pantojinho/StratosCore/docs/MECHANICAL_REQUIREMENTS.md

# Mechanical requirements

Target footprint approximately **80 x 60 mm**, with a **3D-printed enclosure containing the display and two removable 21700 cells**. The first verified fit study proposes an 84 x 60 mm PCB and about 37 mm enclosure thickness. See [mechanical/RF floorplan](MECHANICAL_RF_FLOORPLAN.md). These remain CAD starting envelopes.

Support two removable 21700 cells in a documented 2S holder. Nominal cell class is about 21 mm diameter x 70 mm length; actual selected cell, protection/button top, wrapper, contact travel and holder can exceed those values. A nominal 70 mm cell leaves only 10 mm along the 80 mm target for both contacts and walls. Two nominal diameters already consume 42 mm before separators/holders. Verify tolerance stacks before claiming fit.

A 21.7 mm cell beneath the 4.22 mm display candidate and 1.6 mm PCB consumes 27.52 mm before components, adhesive, gaps or walls. The dimensional reference holder is about 82.2 mm long, so a strict 80 mm board is not feasible. The marketplace holder shown by the owner is an unverified sample candidate until its drawing, wiring and contact ratings are confirmed. The display outline is documented, but FPC bend/connector geometry and sample fit still need verification. Do not freeze connector cutouts or stacked-board design from this arithmetic. Keep batteries away from antenna keepouts and evaluate magnetic bias.

## Required fit study

Build later dummy solids from verified drawings: module/antenna keepout, LCD glass/FPC/connector, cell(s)/holder/removal clearance, PCB/component heights, USB-C, microSD insertion/removal, two button actuators, GNSS antenna alternatives, LoRa U.FL pigtail/SMA bulkhead and ADS-B RF path. Check both orientations, fingers/grip, cable bends and access to recovery/test pads.

Provide positive cell retention, insulated contacts, reverse-insertion prevention, no wrapper damage, and a serviceable battery door. Account for vibration and drops. 3D-print material must be selected against measured internal heat and solar exposure; no flammability, ingress or impact rating is claimed.

SHT40 needs airflow and thermal isolation. BMP581 needs a controlled static pressure path; microphone needs an acoustic path. Rain/dust membranes and slots must be designed with sensor response and manufacturability, not generic decorative openings. Provide antenna strain relief; do not let pigtails cross the ESP module antenna region casually.

Deliverables before placement: dimensioned two-cell envelope and tolerance table, sensor/antenna keepout map, connector access review and printed fit dummy. Files in `mechanical/` are placeholders now; no fabricated STEP/STL is included.
