pantojinho/StratosCore/docs/ASTRA_AGENT_REVIEW_2026_09_24.md

# Astra review of the agent handover — 2026-09-24

Reviewed base: `912894b7dc1f4f4c764267f3bca375b8237b2e48`. Scope: repository and handover consistency, fresh candidate ERC/DRC, selected physical pad/net inventory, cost arithmetic and targeted primary-source checks. This is an independent review of the received agent claims, not a complete electrical, RF, mechanical or manufacturing qualification. No CAD geometry, circuit or project rule was changed.

## Fresh checks

KiCad **10.0.6** loaded the candidate and ran DRC with schematic parity, all track errors and an in-memory zone refill. The board was not saved. The tracked board SHA-256 is `6b77691bea8247bafd36f409d22fdd4d639e2af1f88b8735b518b835c3d2bd30`.

| Check | Observed result |
| --- | --- |
| DRC violations | 328 reported: 209 errors (10 clearance + 199 mask bridges), 119 warnings (118 silkscreen + 1 dangling track) |
| Unconnected items, separate from the violations array | 2 errors, `LORA_RFO` and `LORA_RFI_P` |
| Schematic parity | 0 reported findings |
| ERC | 1 error and 5 warnings; one warning is a library-symbol mismatch |
| Report limits and coverage | 199 mask findings is a reporting lower bound. Five DRC check categories remain disabled in project settings; zero shorts/parity findings do not establish complete correctness |
| Candidate inventory | 277 footprints; U7 pad 17 is GND, 1.68 x 1.68 mm, and its selected footprint is RGT0016C |

Evidence: [DRC with refilled zones](../candidates/claude-oneshot-revA/kicad/reports/astra_audit_2026-09-24/drc_refilled.json), [ERC](../candidates/claude-oneshot-revA/kicad/reports/astra_audit_2026-09-24/erc.json), [pad/net/zone inventory and arithmetic](../candidates/claude-oneshot-revA/kicad/reports/astra_audit_2026-09-24/inventory.json). The new DRC type counts match the tracked September 23 JSON, including **118**, not 117, silkscreen findings.

## Findings and dispositions

| ID | Finding supported by this review | Disposition |
| --- | --- | --- |
| AR01 — major | The candidate README's DRC-error row omitted 10 clearance errors. The received notes call them cosmetic or accepted for prototype. Fresh DRC reports different-net GND/EFUSE_ILM and GND/TP1 VBUS clearance violations, including 0.0773 mm actual against 0.1270 mm required | Correct documentation; keep T3 open. Continuing refinement is not acceptance of these defects |
| AR02 — major | The GND note claims a GND fill island acquired VBUS from TP1 and recommends ignoring zone net names. The actual clearance report identifies **TP1 pad 1**, not a VBUS zone. The inventory contains GND and 3V3_MAIN copper zones, no VBUS zone; a full refill did not remove the violations | Retract the zone-renaming explanation and routing heuristic. Inspect object type, assigned net, UUID and layer; never relabel foreign copper by nearby anchors |
| AR03 — major | D-MASK says S1 needs no assembler query, premium or delay and will retire all 199 findings. The underlying source note explicitly retains assembler/stencil questions and a BMP581 recommendation conflict. A pad-dam calculation alone proves none of those conclusions | Keep S1 as the recorded candidate direction, with implementation and acceptance pending. Do not treat a mask edit as resolving under-sensor routing or all DRC defects |
| AR04 — major | A5/A8 are not implemented: U13 pad 11 remains `EXP_CS_N`; J4 pad 1 remains `LCD_RST_CTRL`. A6 (`SX_NRESET` on U13 pad 13) and A7 (`RP_RUN` on pad 17) already exist in the candidate, but firmware sink-only behavior and the rail decision are not proven by connectivity | Distinguish physical implementation from the decision record. The A8 record specifies a **10 kohm pull-down**, not a pull-up; preserve that polarity and sample-validation condition |
| AR05 — cost evidence | Recalculated the supplied 14 IC prices: USD 59.1021; adding the listed RF/display prices yields USD 113.0461; substituting the unavailable cheaper IMU yields USD 97.9981 = BRL 503.85 at the recorded FX. Arithmetic agrees with the snapshot | This is a partial channel-price scenario, not a globally proven minimum or current quote. Some selected parts have zero stock. BRL 691–726 includes estimated PCB/assembly charges, not import taxes. D24 stays open; no automatic target revision |
| AR06 — reporting | Received notes say 117 silk findings; the tracked and fresh JSON both give 36 overlap + 76 over-copper + 6 edge = 118. The statement that nothing is hidden is too broad: five DRC check categories are disabled | Correct the count and state the configured coverage. No project rules were weakened or changed during this review |
| AR07 — traceability | The candidate decision record links GPIO and cost evidence from the wrong directory. Its final paragraph also suggests the owner must do a manual pass before Astra can act | Repair the evidence links; Astra owns review and execution coordination now. Historical task IDs remain valid |
| AR08 — confirmed with limits | Ground reconnection claims are consistent with fresh DRC reporting only the two LoRa opens. The U7 exposed-pad dimensions and footprint identifier are present in the file | Confirm these narrow facts. They do not validate return-path quality, thermal-via adequacy, power loops, RF behavior or every manufacturer land dimension |

The project-wide documentation also contained obsolete Sol-led / Astra-only-final-CAD instructions. The owner's explicit September 24 direction supersedes them; [D20](DECISIONS.md) and [project control](ASTRA_PROJECT_CONTROL.md) now record Astra's active leadership and delegated worker roles.

## Primary-source spot checks

- **KiCad 10.0 PCB Editor manual**, sections "Working with zones", "Drawing zones" and "Clearances & pad connections", reviewed 2026-09-24: zones have a selected net, keep clearance from other nets and connect according to same-net pad settings. This does not support automatically renaming a GND island to VBUS from an adjacent pad. [Official manual](https://docs.kicad.org/10.0/en/pcbnew/pcbnew.html).
- **Bosch BST-BMP581-DS004-13, revision 1.13, April 2025**, section 8.2, page 69, reviewed 2026-09-24: recommends no traces/vias or solder mask under the sensor, at least 200 micrometres pad separation and 20 micrometres horizontal mask clearance per side. S1's intervening mask therefore needs documented engineering/process disposition; a feasible nominal dam width does not establish manufacturer-conforming assembly. [Manufacturer datasheet](https://www.bosch-sensortec.com/media/boschsensortec/downloads/datasheets/bst-bmp581-ds004.pdf).

No fresh supplier prices, stock, factory commitments, TDK/TI package acceptance or physical performance measurements are claimed by this review. Prior source transcriptions outside these spot checks remain dated evidence requiring their planned reviews.

## Reproduction and next actions

From the repository root, with KiCad 10.0.6 on PATH:

```text
kicad-cli pcb drc --format json --schematic-parity --all-track-errors --refill-zones -o candidates/claude-oneshot-revA/kicad/reports/astra_audit_2026-09-24/drc_refilled.json candidates/claude-oneshot-revA/kicad/StratosCore_Claude.kicad_pcb
kicad-cli sch erc --format json -o candidates/claude-oneshot-revA/kicad/reports/astra_audit_2026-09-24/erc.json candidates/claude-oneshot-revA/kicad/StratosCore_Claude.kicad_sch
python candidates/claude-oneshot-revA/tools/audit_handover.py
```

Use KiCad's bundled Python for the last command. The script reads the PCB and supplied report/price data and writes only the inventory report. DRC descriptions can be localized; type keys and object UUIDs are the comparison evidence.

Successful command execution means reports were generated, not that ERC/DRC passed: the commands above do not request violation-based exit codes. Relative links in the changed Markdown files and `git diff --check` were checked; no tracked KiCad board, schematic, library or project-settings file changed in this audit.

Astra retains T1–T8 and the existing subsystem gates. Next CAD work must resolve actual U3 clearance geometry, validate mask/under-sensor routing, implement A5/A8 after their dependencies, verify A6/A7 behavior, and review power/RF/mechanical details in the GUI against exact source drawings. O05 qualified battery review, controlled display samples, stackup/factory confirmation and independent implementation review remain open. This review does not approve manufacture or energizing.
