pantojinho/StratosCore/docs/OPEN_QUESTIONS.md

# Open questions and closure evidence

This file lists unresolved work only. [Project status](PROJECT_STATUS.md) sets priority; [decisions](DECISIONS.md) records accepted and rejected choices. An accepted direction remains open here when exact engineering or test evidence is still required.

2026-09-24 coordination: Astra now owns engineering closure and delegates bounded tasks to other agents. [The independent handover review](ASTRA_AGENT_REVIEW_2026_09_24.md) confirms that candidate clearance/mask defects and digital implementation gaps remain open; reported proxy decisions do not close O05, display/process, RF, interface or D24 cost evidence gates. [Project control](ASTRA_PROJECT_CONTROL.md) tracks the T1–T8 follow-up queue.

| ID | Status | Type / owner | Question or required closure evidence |
| --- | --- | --- | --- |
| O01 | THREE-LINE MODE PREPARED + SAMPLE GATE | Display / procurement + CAD | Revision-J verifies write-only three-line `101`; obtain controlled TFT-power/FPC clarification, verify XF3M fit/mode on two labeled samples, independently review connector/translator CAD and prototype TPS61169 current, brightness, faults, EMI, touch and shared-bus behavior |
| O03 | PDN CALCULATION CLOSED 2026-09-22; RF/OWNER REVIEW OPEN | GNSS / RF + CAD | GNSS-01 (PR #158) closed the PDN series-impedance budget against the 0.2 ohm u-blox limit (~0.14-0.22 ohm worst, DCR<=0.15 ohm bead fallback) and confirmed the 18-pin net/application table complete: always-on tied 3.3 V VCC/V_IO; open V_BCKP/RESET_N/EXTINT; passive `FXP611.07.0092C` through `U.FL-R-SMT-1(60)` and `TPD1E0B04DPYR`, with no RF bias. Remaining: independent RF/PDN review, owner/RF acceptance of the PROPOSED supply/backup/reset choices, footprints, placement/routing constraints and VNA/test provisions. Cold-start/PPS/AIR4/coexistence and physical VNA results are post-PCBA DVT evidence |
| O04 | PRE-ASTRA DESIGN GATE | ADS-B / RF | Before Astra, freeze the BLB01/TA2003A/ADL5513/MCP6566 topology, exact parts, bias/threshold network, stackup rules, simulation/review evidence and conducted-test provisions for sensitivity, blockers, gain, pulse timing and coexistence. Physical measurements are post-PCBA DVT evidence |
| O05 | OWNER ACCEPTED; REVIEW BLOCKED | Power / qualified reviewer | Resolve BQ25887 autonomous charge after reset, fail-safe `CD` gating, charger/common-protector ground and cutoff recovery, charge-under-load termination, exact holder/cells/FETs/fuse/NTCs and fault limits before schematic commitment or energizing |
| O06 | USB INPUT + RAIL INVENTORY CLOSED 2026-09-22; CHARGER ENGINEERING OPEN | Power / Sol + qualified reviewer | D21 requires operation while charging. PWR-02 (PR #147) closed the TPS259474L eFuse network (RILM/UVLO/OVLO/dVdt) and the TUSB320LAI GPIO-mode default-current-only sink policy; ITIMER remains TBD pending the charger's worst-case inrush/input-capacitance transient. PWR-04 (PR #157) closed all `3V3_MAIN` rail loads and startup sequencing (~1,413 mA simultaneous worst-case, 59% of the 3 A buck rating with margin). Remaining: select exact holder/protection topology and calculate BQ25887 charger setpoint, buck, balancing, state estimation and charge-under-load termination. No batteryless operation or USB PD is proposed |
| O07 | AUDIO NETS RECONCILED AS PROPOSAL; APPLICATION/FOOTPRINT REVIEW OPEN | Audio/power/CAD + test | AUD-01 (PR #159) pinned TXU0202 channel directions. The 2026-09-22 [audio-domain review](AUDIO_DOMAIN_REVIEW.md) found shared `1V8_LOGIC` versus switched-audio inconsistency. Integrator reconciled the preferred net plan: keep TFT on `1V8_LOGIC`; switch only T5838 VDD and TXU0202 VCCB/OE via `1V8_AUDIO_SW`. Exact TPS22918 CT/QOD/ramp/drop, off-state pins and boot sequence remain before schematic entry; do not treat the candidate as a frozen circuit. The TXU0202 footprint requires independent exact-MPN review and T5838 acoustic land is deferred; port/gasket, optional DNP and test plan remain. PDM/RF measurements are post-PCBA evidence |
| O08 | PROTOTYPE GATE | Mechanical | Verify the 84 x 60 mm PCB and approximately 88 x 64 x 37 mm enclosure with exact component drawings and a printed fit dummy |
| O09 | PREFERRED INTERCONNECT - U.FL CAD REVIEWED | RF/mechanical / RF + CAD | Review P20/P25; U.FL copper/paste and board-cut-out comparison is complete; independently compare the CAB.721 drawing, obtain U.FL assembler approval, fit all cables/antenna in the enclosure dummy, calculate/VNA-check each 50-ohm path and verify port labeling, tool access, strain relief and coexistence |
| O10 | STACK VERIFIED; SOLVER GATE OPEN | PCB/manufacturer | JLCPCB officially documents JLC04161H-3313 replacing the former 2313 (same thickness/Dk 4.1, verified 2026-09-17 with candidate geometries in PCB_STACKUP.md). Before Astra routing, obtain reproducible factory-solver 50/90-ohm geometries and tolerances. The actual order ticket, coupon and TDR are post-layout manufacturing controls |
| O11 | ENGINEERING ANALYSIS CLOSED 2026-09-22; OFF-STATE REVIEW REMAINS | Hardware / Sol + CAD + test | D22/P26 applied via PR #140: GPIO/net map updated with the TUSB320LAI GPIO-mode wiring (SLLSEQ8D Rev D), reduced participant set evaluated, pull-up 2.2 k ohm +/-1% proposed with a window non-empty to the 400 pF ceiling, expansion-cable limit declared <=150 pF and stuck-bus recovery assigned. DIG-03 (PR #149 + polarity fix #152) fixed the switched-domain default: pull-down + active-high EN per TPS22918 leaves every domain OFF through expander reset/hang/power loss (`*_EN` net rename recorded for Astra). Remaining: per-device off-state review (touch, BQ25887, switched domains), post-placement `Cb` recount, independent net-matrix review (SYS-04) and the post-PCBA rise-time/VOL validation |
| O12 | HOST CONTRACT TESTED; PRE-ASTRA INTERFACE GATED | RP2040 interface / Sol | The host-side UART framing behavior passes 20 framing tests plus the four existing capture-model tests: fixed payload shapes, CRC16-CCITT, rolling sequence, 64-bit timestamp reconstruction, declared overflow, resynchronization after garbage/corrupt headers/CRC and a fragmented 200-contact stream. [SYS-03 contract](CONCURRENCY_CONTRACT.md) calculates 921600-baud/8N1 line headroom and UART blackout buffering but leaves actual DMA/PIO/ring sizing and timing TBD. Before Astra, freeze pins, clocks, PIO/DMA contract, exact burst/throughput and test access. Real-hardware sustained-link tests remain post-PCBA |
| O13 | 8 H OWNER TARGET ACCEPTED; ANALYTICAL BUDGET CONSISTENT, MEASUREMENT OPEN | Power/product | D25 sets 8 h on the two-cell pair for primary use. The conservative 1.935 W FLIGHT allowance gives an estimated 10.72 h with two example 5 Ah cells under the documented 80% usable/90% conversion assumptions, so the model clears 8 h but proves no actual runtime. Before Astra, close primary-use duty/brightness and cell/thermal assumptions; real rail efficiency, cell behavior and full-profile runtime are measured post-PCBA |
| O14 | DEFERRED | Firmware/license | Select firmware framework and define MeshCore mode/port/dependencies after the hardware baseline; complete transitive license audit |
| O15 | CONTINUOUS | Maintainer/license reviewer | Record any reused circuit/code at file level; resolve ADSBee GPL and avBadge uncertainty before reuse |
| O16 | BMP581 RETAINED; INDICATIVE 10,000 FT TEST/ENVIRONMENT OPEN | Product/test | D25/D29 now use ~10,000 ft as the realistic case and keep BMP581 as secondary indicative altitude/vario. The former 30,000 ft guarantee was withdrawn; [P27](BAROMETER_30K_PROPOSAL.md) was rejected. Define actual board temperature, reference pressure/calibration, vent behavior, bench pressure/vario test and invalid/out-of-range display/logging. Assess exposed flight/balloon dynamics and temperature separately; do not claim 30,000 ft coverage |
| O17 | DEFERRED | Product/firmware | Set acquisition rates, SD capacity, audio format and allowed data loss after hardware interfaces and power profiles are stable |
| O18 | OWNER INPUT + RF TEST | ADS-B/product | Define sensitivity, range, contact/stale-time targets and a repeatable conducted/field test plan |
| O19 | CORRECTED CANDIDATES; INDEPENDENT / ASSEMBLER REVIEW OPEN | Sensors/procurement + CAD | The 2026-09-23 [correction record](FOOTPRINT_CORRECTIONS_2026_09_23.md) supersedes the old MMC5983MA/BMP581 dimensional-pass claims: radial land centers and provisional paste are repaired, top-view pin maps rechecked, and pairwise copper gaps pass at 0.200 mm. Independently review the revised files and assembler mask/paste/stencil choices. SNS-02 placement constraints remain in the floorplan; final routing, magnetic/pressure-port placement and fit-dummy checks remain open |
| O20 | IN PROGRESS - EXACT PACKAGE REVIEW | Digital/GNSS/RF CAD | See [corrections and rejected drafts](FOOTPRINT_CORRECTIONS_2026_09_23.md). The old TXU0202 DGS and TPS259474L RPU files must not be assigned. Exact DCU copper was rederived and checked; exact RPW polygon/stencil still needs closure. The original TCA9535 body is 4.4 x 7.8 mm, not the unpublished 6.4 mm draft. Re-review all DIG-04 parts against drawings, reconcile library/process gates and finish deferred USB4105/BM12B/SKSCLCE010/ST1633I/T5838 footprints. DIG-01/02 electrical work and DM3/test-access gates retain their separate scope |
| O21 | OWNER CLASSIFICATION ACCEPTED; REGULATORY PLAN OPEN | Regulatory/owner | D23 defines Rev A as a personal, non-commercial, open-community hobby prototype. Determine the applicable ANATEL operating path for 915 MHz TX and the 2.4 GHz/1.575 GHz/1.090 GHz receivers; the classification does not itself authorize radio operation |
| O22 | OWNER HOBBY USE CASES ACCEPTED; FLIGHT PLAN OPEN | Regulatory/owner | D25 includes desk/car/protected unpressurized cabin use and possible experimental drone, model-aircraft, balloon, ultralight, hang-glider and paramotor installation. Determine the applicable aviation/balloon rules, tracking, authorization and recovery obligations for any actual flight after each installation envelope and built mass are known; no design target mass is imposed |
| O23 | ACCOUNTING BOUNDARY ACCEPTED; QUOTES OPEN | Product/procurement | D24 sets an average ceiling of BRL 200 per unit for the first five Chinese PCBAs including display/touch, excluding local cells/enclosure, freight and taxes. Obtain actual five-unit assembly/display quotes and record whether the target is feasible without silently removing locked Rev A functions |
| O25 | OWNER POLICY ACCEPTED; LOCAL PLAN OPEN | Manufacturing/test | D28 selects factory PCBA assembly only, then local USB-C flashing and testing with no factory firmware or credentials. Define the local programming fixture/procedure and board-identification method; retain accessible SWD recovery |
| O27 | PRE-ASTRA ENGINEERING BASELINE | Sourcing/BOM | Convert `bom/preliminary_bom.csv` into a frozen engineering parts baseline: every fitted/DNP item and passive needs exact specification, package, approved footprint, planned quantity and sourcing status. The [2026-09-22 gap audit](BOM_BASELINE_GAP_AUDIT.md) verified 58 rows, no quantity column, 7 literal `MPN=TBD` rows plus family-only `CELL_PROTECTION`, 37 `JLCPCB/LCSC Part Number=TBD` rows (correcting the earlier 36), and an incomplete aggregate `PASSIVES_DEBUG` row. BOM-02 (PR #168) recorded 6 dated SNAPSHOT and 19 authorized-channel CHANNEL-ONLY groups; these are not current five-unit quotes or assembler acceptance. Astra produces annotated references/quantities only after the engineering baseline; final orderable BOM follows review |
| O28 | PRE-PLACEMENT MATRIX FROZEN 2026-09-22; POST-LAYOUT FIXTURE REVIEW OPEN | Test/DFT | DFT-01 (PR #161) froze the 17-row pre-placement DFT coverage matrix in `manufacturing/test/README.md`: nets requiring pads, programming/SWD/BOOTSEL access, RF injection, pad family/minimum geometry, permitted face, fixture pitch, current limits and the rail/current measurement points feeding O13, all traced to accepted deliverables (DIG-01/02/03, PWR-02/04, GNSS-01, AUD-01, SYS-01, P25). Protection-FET access deliberately not defined (O05/PWR-03). Remaining: Astra assigns references/coordinates during placement; physical probe access and fixture feasibility are reviewed after layout; production screening limits need measured data |

## Recently closed owner decisions

| ID | Closed | Outcome |
| --- | --- | --- |
| O02 / P07 | 2026-09-13 | Owner replaced ATGM332D-5NR32 with MAX-M10S-00B for the balloon altitude envelope |
| P08 / P14 | 2026-09-13 | Owner rejected independent 1S bays and accepted two removable matched 21700 cells in 2S with one balanced charger and common protection direction |
| D21 / O06 policy | 2026-09-21 | Owner requires normal operation while USB charging; exact safe charge-under-load design remains open |
| D22 / P26 policy | 2026-09-21 | Owner accepted 100 kHz shared I2C and TUSB320LAI GPIO mode; SYS-01 implements and reviews the electrical details |
| D23 | 2026-09-21 | Owner classified Rev A as a personal, non-commercial, open-community hobby prototype |
| D26 / O24 | 2026-09-21 | Owner will source cells locally; shipping the prototype with cells is outside the current scope |
| D27 / O26 | 2026-09-21 | Owner requires no conformal coating, ingress qualification or special environmental protection for Rev A |

P14 is closed as a product direction but O05/O06 remain open engineering and review gates. The qualified electrical/battery review is mandatory before the exact topology is frozen, entered as a committed schematic or energized.
