pantojinho/StratosCore/docs/PROJECT_STATUS.md

# Project status

Last updated: 2026-09-24. Current phase: **Astra-led hardware engineering closure and candidate refinement**.

Astra has already assumed full technical leadership, coordination, review and integration of StratosCore, as accepted by the owner in revised D20. Claude, Hermes, Sol and other AI agents execute bounded tasks delegated by Astra. The immediate objective remains exact component/application/interface closure, candidate correction and hardware/PCBA readiness. [Astra project control and agent handover](ASTRA_PROJECT_CONTROL.md) records the received summary, its evidence boundaries and the T1–T8 candidate queue.

Execution is coordinated through the [Astra-led engineering workboard](PRE_ASTRA_WORKBOARD.md). Parallel agents follow the [swarm protocol](SWARM_PROTOCOL.md); Astra as integrator reconciles shared status, decision, open-question, handoff and BOM files. The reusable [Astra execution prompt](ASTRA_EXECUTION_PROMPT.md) remains **NOT READY** for final frozen-baseline implementation until its input manifest and every handoff gate are complete.

## Completed and verified

| Area | Current result | Evidence boundary |
| --- | --- | --- |
| Repository foundation | Licensing, contribution rules, source/reuse tracking and direct-to-main workflow established | Does not release hardware for manufacture |
| Rev A product baseline | Compute, display class, sensors, LoRa, ADS-B/RP2040, storage, audio provision, expansion and four-layer construction recorded | Exact open parts remain below |
| Display evidence | C1 serial straps verified; write-only three-line `101` preferred; exact XF3M lands and AXC/LVC/backlight starting circuits documented | Controlled TFT power/FPC clarification, samples, connector footprints, independent CAD and prototype tests still gate release |
| GNSS product decision | MAX-M10S-00B accepted; pin/application evidence and P20 passive antenna/U.FL/ESD proposal reviewed; manufacturer-derived copper/mask/T-paste footprint parses in KiCad, passes its automated geometry audit and completed an independent dimensional review | Assembler paste approval, RF/PDN review, antenna fit and prototype tests remain |
| Battery product decision | Two removable matched 21700 cells in 2S; one balanced charger and common protection direction accepted | Exact circuit needs qualified electrical/battery review |
| Owner operating/product inputs | Operation while charging; 100 kHz shared I2C with TUSB320LAI in GPIO mode; personal non-commercial community prototype; five-unit BRL 200 average PCBA-plus-display/touch target; desk/car/protected unpressurized cabin and possible experimental hobby flight uses; ~10,000 ft realistic, 30,000 ft exploratory; BMP581 indicative backup; 8 h minimum on two 21700 cells; local USB-C flashing/testing; locally sourced cells; no coating/ingress qualification | P27 LPS22HBTR replacement rejected; sensor temperature, exposed-flight/balloon envelopes, ADS-B targets, cost feasibility and local test procedure remain open |
| ESP32 compute | ESP32-S3-WROOM-1-N16R8 entry, decoupling/reset and complete GPIO allocation present in KiCad | Board-level concurrency and boot-state validation remain |
| Sensors | All four logical entries are present. A fresh drawing comparison found and corrected MMC5983MA/BMP581 baseline land geometry errors in `9e909f3`; see the [correction evidence](FOOTPRINT_CORRECTIONS_2026_09_23.md). SNS-02 (PR #167) froze dimensioned, zoned placement constraints in `MECHANICAL_RF_FLOORPLAN.md`. A [BMP581 validation plan](BMP581_VALIDATION_PLAN.md) distinguishes indicative ~10,000 ft design/test work from post-PCBA measurement | Independent review of corrected files, candidate embedded footprint reconciliation, assembler mask/paste disposition, proposed data-validity contract and fit-dummy/routing conformance remain |
| ADS-B digital feasibility | Host timing/CRC fixture passes four tests; UART framing behavior passes 20 additional host tests | UART throughput and RP2040 PIO/DMA hardware remain unproven; analog RF sensitivity is also open |
| Remaining support candidates | Exact candidates documented for main/quiet/1.8 V rails, PDM audio, USB-C/signal ESD, expansion, buttons, slow I/O and RF interconnects; historical parse/export and dimensional-review records exist, but the sensor/DCU/RPW defects mean those records do not establish blanket readiness. AUD-01 closed TXU0202 channel directions and mic supply/clock/acoustic evidence; later integration found its direct-`1V8_LOGIC` assignment conflicted with audio switching, so [AUD-02](AUDIO_DOMAIN_REVIEW.md) prefers a separate `1V8_AUDIO_SW` branch pending exact application review. DIG-04 (PR #164) added eight standard-package footprint candidates | DM3 enclosure/process closure, assembler approvals, audio switch CT/QOD/ramp/off-state, port/gasket (MECH-02/03), VBUS/protection and board tests remain open. The new exact-DCU candidate and remaining DIG-04 exact-MPN reviews plus five deferred footprints (USB4105, BM12B, SKSCLCE010, ST1633I, T5838) remain open |
| KiCad structure | Root plus eight sheets parse in KiCad 10; latest ERC has zero violations | Several sheets are intentional holds, not completed circuits |
| Mechanical planning | 84 x 60 mm PCB and about 88 x 64 x 37 mm two-cell enclosure are starting envelopes | Printed dummy, exact holder and display connector/sample fit remain |
| Manufacturing plan | Four-layer Chinese PCBA workflow and release gates documented. BOM-02 (PR #168) consolidated the per-MPN sourcing evidence register 2026-09-22 (`bom/SOURCING_EVIDENCE.md`): 6 dated SNAPSHOT rows plus 19 authorized-channel CHANNEL-ONLY groups, no fabricated stock/price. The [BOM gap audit](BOM_BASELINE_GAP_AUDIT.md) counted 58 planning rows, 7 literal MPN TBDs, family-only protection, 37 supplier-ID TBDs and no planned quantities | No Gerbers, CPL or engineering parts baseline exist yet; engineering baseline work is O27/BOM-01/03. DFT-01 froze 17-row pre-placement coverage; Astra still assigns references/coordinates. Purchase-time recheck remains authoritative; annotated/final orderable BOMs follow capture/review |

## Out-of-baseline comparison candidate (2026-09-23)

At the owner's explicit request, a complete one-shot KiCad candidate (12-sheet schematic, routed 4-layer 60 x 84 mm PCB, display/2S-cell/enclosure 3D) was generated in [`candidates/claude-oneshot-revA/`](../candidates/claude-oneshot-revA/README.md) for comparison with the Astra pass. It is **not** a baseline, does not close any gate below and keeps every unverified value `TBD`. Its [issue list](../candidates/claude-oneshot-revA/docs/ISSUES.md) records baseline defects that need independent review in `hardware/footprints/`: MMC5983MA pad centres (+/-1.05 mm vs MEMSIC 2.550 mm centre-to-centre, corner pads overlap), BMP581 pad centres (+/-0.6 mm vs Bosch 1.525 mm, 0.04 mm corner gap), TXU0202 footprint uses the DGS 3 x 3 mm package instead of DCU, TPS259474L footprint uses RPU instead of RPW, and BM12B-GHS-TBT is a vertical header, plus GPIO/expander allocation gaps (EXP_CS, SX1262 NRESET, RP2040 RUN, touch reset).

The initial 2026-09-23 KiCad 10.0.6 review recorded 1 ERC error/4 warnings, 1 DRC error/579 warnings, 11 unconnected items and zero schematic-parity issues; these are historical counts. The received handover at `912894b` reports 2 remaining LoRa connections, 0 shorts/parity findings, 10 U3 clearance findings, 199 reported mask bridges (report limit), 117 silkscreen findings and 1 dangling track. Astra's [independent September 24 review](ASTRA_AGENT_REVIEW_2026_09_24.md) reran DRC with zone refill and confirmed those counts except silkscreen: the correct total is 118. It recorded 209 DRC errors and 119 warnings, plus the two unconnected items separately, and ERC 1 error/5 warnings. A5/A8 and mask choices still need CAD implementation; A6/A7 connectivity exists but behavior and rail review remain open. The [independent review](CLAUDE_CANDIDATE_INDEPENDENT_REVIEW.md) and [bounded Astra candidate-refinement prompt](ASTRA_CANDIDATE_REFINEMENT_PROMPT.md) allow evidence-backed correction work now while the final execution handoff remains blocked.

## Remaining gates for final baseline implementation and release

| Priority | Gate | Astra-coordinated work and external dependencies | Closure evidence |
| ---: | --- | --- | --- |
| 1 | Exact display | Obtain controlled Orient TFT-power/FPC clarification and two labeled samples; validate provisional three-line `101` mode and XF3M fit; independently compare CAD and prototype translation/backlight | Verified footprints plus backlight, address, power, touch/readability, fault, EMI and shared-bus results |
| 2 | 2S power | D21 requires operation while charging and D26 fixes local removable cells. PWR-02 closed the USB input application 2026-09-22 (PR #147): TPS259474L eFuse network exact (RILM/UVLO/OVLO/dVdt; ITIMER TBD at O06), TUSB320LAI default-current-only policy fixed from GPIO-mode facts. PWR-04 closed the `3V3_MAIN` rail load inventory 2026-09-22 (PR #157): simultaneous worst-case ~1,413 mA (59% of the 3 A buck rating with 25% margin), every row sourced or declared ALLOW, regulator passives pinned and sequencing recorded. Remaining: accept exact cell/holder; resolve BQ25887 autonomous-start hardware gating, charger/protector ground/cutoff conflict and charge-under-load termination; close protection/FET/fuse/NTCs, buck, state estimation and every fault state | Qualified reviewer signs the complete schematic plan and fault limits before KiCad commitment |
| 3 | GNSS implementation package | GNSS-01 closed the MAX-M10S PDN calculation 2026-09-22 (PR #158): series-impedance budget against the 0.2 ohm u-blox limit (~0.14-0.22 ohm worst, DCR<=0.15 ohm bead fallback), module-local capacitance and soft-start ramp disposition; 18-pin net/application table confirmed complete. Obtain assembler approval of the independently reviewed MAX-M10S T-paste pattern; obtain independent RF/PDN review and owner/RF acceptance of the PROPOSED supply/backup/reset choices; close remaining RF calculations, keepout and test provisions. Physical VNA/cold-start/PPS/AIR4/coexistence results remain post-PCBA | Accepted choices, independently reviewed footprint, antenna fit/layout constraints and executable validation plan |
| 4 | Remaining digital parts | Datasheet-level evidence closed 2026-09-17 (W25Q JVSIQ ordering/QE/BOOTSEL/XIP, RP2040 boot/circuit, ABM8-272-T3 reference circuit). DIG-01 closed the RP2040 reset/BOOTSEL/SWD/oscillator circuit 2026-09-22 (PR #144). DIG-03 closed the TCA9535 16-port map 2026-09-22 (PR #149 + polarity fix #152): pull-down + active-high EN per TPS22918 leaves every switched domain OFF through expander reset/hang/power loss. DIG-02 closed microSD power/signal/ESD/card-detect/power-fail 2026-09-22 (PR #154): switched `3V3_SD` behind the DIG-03 enable, SPI-mode SD_CS->DAT3 mapping, socket-edge ESD array (device-level claim only). AUD-01 closed the T5838/TXU0202 audio application 2026-09-22 (PR #159): pin-complete translator channel directions, `1V8_LOGIC`-referenced OE rail-valid policy, mic clock window (2.0-3.7 MHz) and current input (310/340 uA typ/max), with DS section 9 acoustic land/hole/paste rules handed to DIG-04 verbatim. DFT-01 froze the pre-placement DFT coverage matrix 2026-09-22 (PR #161, O28). DIG-04 delivered the standard-package support-footprint set 2026-09-22 (PR #164), but exact-package acceptance was reopened on 2026-09-23 (see the correction record): all 17 project footprints parse/export in KiCad 10.0.6, eight new candidates carry per-file provenance to the copied KiCad-library source and TI package drawing class, five custom/connector footprints (USB4105, BM12B-GHS-TBT, SKSCLCE010, ST1633I, T5838 acoustic land) deliberately deferred. Before final baseline implementation, close DM3 enclosure/process, residual U.FL process/tool gates, per-pin off-state proof, insertion-surge measurement (PWR-04), the exact-MPN second pass on the eight new DIG-04 footprints, the five deferred footprints and Astra reference/coordinate assignment for the DFT matrix. Physical bench tests remain post-PCBA | Orderable reviewed MPNs, pin maps, footprints, interface/voltage evidence and test provisions |
| 5 | Sensors | ICM-42688-P retains its recorded dimensional review. MMC5983MA/BMP581 land centers were corrected after the old review missed defects; independent review of the revised files and assembler process approval remain open. SNS-02 froze placement constraints 2026-09-22 (PR #167). D29 retains BMP581 as an indicative backup for ~10,000 ft realistic use; 30,000 ft is exploratory. [BMP581 validation plan](BMP581_VALIDATION_PLAN.md) drafts pressure/vario and invalid-data tests. [P27](BAROMETER_30K_PROPOSAL.md) is rejected history | Review/accept validity contract, sensor environment, assembler approval and fit-dummy/routing conformance. Physical pressure/vario characterization is post-PCBA |
| 6 | LoRa RF | AN1200.40 Rev 1.1 evidence recorded: E449V01A 4-layer TCXO design proposed as starting topology, matching/notch/pi-filter topology and RX balun documented, DC-DC + crystal proposal with TCXO/DIO3 fallback, PE4259-class switch proposal, conducted test outline. Remaining: exact E449 regional BOM values (drawing-embedded) and RF CAD | Reference revision BOM values, independent CAD, simulation/stackup inputs and conducted-test plan |
| 7 | ADS-B RF | BLB01/TA2003A/ADL5513/MCP6566 bias and loss figures transcribed. ADSB-01 (PR #142) froze the base `MCP6566T-E/OT` pin map and a proposed 2.2 kohm pull-up; R/U variants are non-drop-in alternatives. Before final baseline implementation, close the threshold (OWN-09), remaining topology, simulation, stackup rules and conducted-test provisions. Physical RF measurements remain post-PCBA | RF review plus testable schematic, simulation evidence and conducted acceptance limits |
| 8 | PCB/mechanical inputs | JLC04161H-3313 stack verified from official JLCPCB pages 2026-09-17 (3313 replaced 2313, same thickness/Dk; candidate 50/90-ohm geometries computed and recorded in PCB_STACKUP.md). D27 selects no coating or ingress qualification. Before final baseline implementation, obtain factory-solver impedance geometry, outline/connectors/keepouts and fit dummy. The actual order ticket, coupon and TDR follow layout | Frozen stack/solver rules and signed mechanical fit review |
| 9 | System-level electrical review | D22/P26 applied 2026-09-22 (PR #140): 100 kHz shared I2C with TUSB320LAI in GPIO mode, pull-up window non-empty to the 400 pF ceiling (2.2 k preferred), expansion-cable reserve <=150 pF declared and stuck-bus recovery assigned; SYS-01 accepted. PWR-04 closed the peak-load inventory (~1,413 mA simultaneous allowance, not measurement). DIG-03 fixed TPS22918 enables to active-high/pull-down. DSP-02 display reset wording was reconciled with TI SCES296AG Rev AG section 7.4 (low input asserts reset). The audio-domain review prefers a separately switched `1V8_AUDIO_SW` branch, with exact CT/QOD/ramp/off-state still open. A [concurrency contract](CONCURRENCY_CONTRACT.md) now records resource arithmetic and an executable post-PCBA stress outline, with numeric deadlines/buffers still TBD. DFT-01 froze 17-row pre-placement access coverage. Remaining: full off-state/boot matrix (SYS-02), quantitative concurrency closure (SYS-03), independent review (SYS-04), Astra DFT references/coordinates and post-layout access review | Independently reviewed net/interface matrix with no unresolved collision |
| 10 | Regulatory and product inputs | D23 classifies Rev A as a personal, non-commercial, open-community hobby prototype; D24 bounds five PCBA-plus-display/touch units to BRL 200 average excluding local cells/enclosure, freight and taxes; D25/D29 define ~10,000 ft realistic use with indicative BMP581 backup, 30,000 ft exploratory, and 8 h minimum; D26/27 close local cells and no environmental qualification; D28 selects local USB-C flashing/testing | Temperature/installation limits, balloon/exposed-flight envelope, ADS-B targets, cost feasibility, local test procedure and applicable regulatory plan remain open; hobby status is not an assumed exemption |

## Astra's active responsibility and final implementation gate

Astra owns engineering and candidate work now. Final frozen-baseline KiCad implementation requires all applicable entry-gate evidence and [the final handoff](ASTRA_HANDOFF.md) marked **READY**. Astra coordinates library integration, schematic capture, annotation, ERC, PCB setup, placement, routing and DRC within the authorized scope. An `ENGINEERING_RETURN` pauses dependent edits and remains Astra's responsibility to resolve or delegate; it does not transfer project control to another agent.

## Independent implementation review and release

An independent review must inspect the completed schematic and PCB, especially power and RF. Only then generate and cross-check Gerbers, drill files, fabrication notes, orderable BOM, component-placement file, assembly drawings and programming/test instructions. The project owner must explicitly accept the manufacturing release before an order is placed.
