pantojinho/StratosCore/docs/FOOTPRINT_REVIEWS_DIGITAL.md

# Footprint reviews: RP2040 support and storage parts

Status: reviewed through 2026-09-17. Project-owned footprints for the RP2040 support and storage candidates. Provenance and residual release gates are recorded per part; anything not yet verified against the exact manufacturer drawing is explicitly marked PENDING.

## Winbond `W25Q128JVSIQ` — boot flash

- **Footprint:** `hardware/footprints/Winbond_W25Q128JVSIQ_SOIC-8_5.3x5.3mm_P1.27mm.kicad_mod`
- **Controlling sources:** Winbond W25Q128JV data sheet Rev M, 2024-12-24, sections 3.1/10.1/11.1, and Winbond `AN0000009` Serial Flash PCB Layout Guidelines Rev 2.1, 2020-06-12, pages 6-7.
- **Key geometry:** package-S body 5.18-5.38 mm, lead span 7.70-8.10 mm and 1.27 mm pitch. Manufacturer copper is `1.90 x 0.80 mm` at X = +/-3.95 mm; the distinct 0.10 mm-stencil aperture is `1.80 x 0.70 mm` at X = +/-4.00 mm. Y centers are +/-1.905 and +/-0.635 mm.
- **Review correction 2026-09-17:** replaced the earlier generic KiCad 1.625 x 0.65 mm roundrect land, expanded the courtyard to contain the manufacturer pattern, retained correct top-view pin order and rewrote the project footprint as an original geometric transcription.
- **Independent second pass:** confirmed package/pin orientation, all copper/paste sizes and centers, body/lead envelopes and courtyard containment against both Winbond sources with no critical/high/medium mismatch; KiCad 10.0.6 export returned success.
- **Verdict:** manufacturer-derived candidate passes dimensional review and KiCad parse/export. Solder-mask expansion, courtyard excess and assembler process remain release gates; status-register/boot bring-up remains a prototype gate.
- **Supply snapshot:** DigiKey showed 57,555 units at USD 4.21 (quantity 1) on 2026-09-14 (project snapshot; recheck at purchase).

## Abracon `ABM8-272-T3` — 12 MHz RP2040 reference clock

- **Footprint:** `hardware/footprints/Abracon_ABM8-272-T3_Crystal_SMD_3225-4Pin_3.2x2.5mm.kicad_mod`
- **Controlling sources:** exact-MPN Abracon source-control drawing `456603 Rev B`, dated 2024-09-16, for part identity/package/electrical data, plus the official ABM8 series sheet revised 2020-07-29 for the recommended land pattern. The previous TXC-derived generic KiCad land is no longer the project geometry.
- **Manufacturer land:** four rectangular 1.30 x 0.70 mm lands. Column centers are X = +/-1.15 mm, row centers are Y = +/-0.875 mm, giving a 1.00 mm horizontal inner gap and 1.05 mm vertical inner gap. In the rendered PCB top view pin 1 is lower-left, pin 2 lower-right, pin 3 upper-right and pin 4 upper-left; the CAD pin-1 mark is explicit because package chamfers must not be used as an electrical-numbering inference.
- **Paste/mask boundary:** 1:1 paste and mask are a project process starting point, not a manufacturer stencil recommendation. The PCBA assembler must approve mask expansion, apertures and stencil thickness before release.
- **Independent second pass:** review on 2026-09-15 rejected the old 1.4 x 1.2 mm generic pads, confirmed the exact manufacturer geometry above and found no remaining dimensional conflict in the corrected candidate. KiCad parsing/export and the geometry audit are required below.
- **Application context:** Raspberry Pi's *Hardware design with RP2040* recommends this exact crystal with two 15 pF load capacitors and a 1 kohm series damping resistor; oscillator startup, drive and timebase remain prototype tests.
- **Supply snapshot:** DigiKey showed 29,393 units at USD 0.71 (quantity 1) on 2026-09-14 (project snapshot; recheck at purchase).

## Hirose `DM3AT-SF-PEJM5` — microSD socket

- **Footprint:** `hardware/footprints/Hirose_DM3AT-SF-PEJM5_microSD_HC.kicad_mod`
- **Controlling source:** exact Hirose drawing `0000947170 / EDC-325165-00-00`, revision 4, dated 2026-08-01, for `DM3AT-SF-PEJM5`; the earlier download identifier 44099 is obsolete.
- **Key geometry:** the independent 2026-09-15 comparison confirmed pads 1-8, card-detect pads 9-10, four shell lands, top-board orientation and electrical pin mapping against the exact drawing.
- **Mechanical/process result:** the drawing's C0.15 +/-0.05 callout is a connector-terminal feature inside the rectangular 1.3 x 1.9 mm recommended PCB land, so the PCB pad remains rectangular. The footprint now records the 11.0 mm card width at X = -5.925..+5.075, the 0.8 mm inward overstroke edge at Y = 8.925, locked front edge at Y = 9.725 and ejected front edge at Y = 13.725 on `Cmts.User`. Paste remains a 1:1 project starting point; the drawing calls out a 0.12 mm stencil but does not authorize a different aperture.
- **Verdict:** electrical lands/pin map and the operational card envelope are dimensionally reviewed. Assembler paste approval, final enclosure clearance/access and board-level ESD/power-fail testing keep this footprint gated.
- **Supply snapshot:** DigiKey regional pages showed about 29,700 units at about USD 5.20 (quantity 1) on 2026-09-14 (project snapshot; recheck at purchase).

## Process note

Manufacturer drawings control every project-owned footprint. The W25Q128 and ABM8 geometries have replaced earlier generic library lands, and the DM3 comparison has identified its remaining shell/mechanical work. The sensors/GNSS/RF footprints are covered by [FOOTPRINT_REVIEWS_SENSORS_GNSS.md](FOOTPRINT_REVIEWS_SENSORS_GNSS.md).

## Support-part footprint candidates (DIG-04, added 2026-09-22)

Eight additional support-part footprints were added from the **official KiCad 10.0.6 standard library** (files copied unmodified from the installed `kicad-footprints` package, Ubuntu `kicad` 7.0.11/10.0.6 library set, whose geometries are derived from JEDEC/IPC-7351B and the named TI package drawings). Provenance class for all eight: **standard-package geometry, not an exact-MPN manufacturer-drawing derivation** — they are not approved for assignment; exact TXU0202 and TPS259474L package mismatches were later confirmed, and each still requires the same independent pad-by-pad comparison against the exact-MPN manufacturer drawing before prototype release, plus the standing assembler mask/paste gate. The library file name of the copied source is recorded per footprint so the derivation is auditable:

| Project file | Copied from KiCad 10 library | Covers (package / TI drawing class) | Delivering circuit |
| --- | --- | --- | --- |
| `TI_DBV0005A_SOT-23-5_TPS7A20.kicad_mod` | `Package_TO_SOT_SMD.pretty/SOT-23-5.kicad_mod` | SOT-23-5 (DBV0005A) — TPS7A2030/TPS7A2018 | PWR-04 rail rows |
| `TI_DBV0006A_SOT-23-6_TPS22918.kicad_mod` | `Package_TO_SOT_SMD.pretty/SOT-23-6.kicad_mod` | SOT-23-6 (DBV0006A) — TPS22918DBVR x3 | DIG-03/PWR-04 switched domains |
| `TI_DCK0005A_SC-70-5_TPS61169.kicad_mod` | `Package_TO_SOT_SMD.pretty/SOT-353_SC-70-5.kicad_mod` | SC-70-5 (DCK0005A) — TPS61169DCKR | Backlight |
| `TI_DGS0010A_VSSOP-8_3x3mm_P0.65mm_TXU0202.kicad_mod` | `Package_SO.pretty/VSSOP-8_3x3mm_P0.65mm.kicad_mod` | REJECTED for TXU0202DCUR; use the reviewed DCU candidate after process gates | AUD-01 |
| `TI_PW0024A_TSSOP-24_4.4x7.8mm_P0.65mm_TCA9535.kicad_mod` | `Package_SO.pretty/TSSOP-24_4.4x7.8mm_P0.65mm.kicad_mod` | TSSOP-24 (PW0024A) — TCA9535PWR | DIG-03 |
| `TI_RWB0012B_X2QFN-12_1.6x1.6mm_TUSB320LAI.kicad_mod` | `Package_DFN_QFN.pretty/Texas_X2QFN-12_1.6x1.6mm_P0.4mm.kicad_mod` | X2QFN-12 1.6x1.6 (RWB0012B) — TUSB320LAIRWBR | D22 GPIO-mode wiring |
| `TI_RPU0010A_VQFN-HR-10_2x2mm_TPS259474L.kicad_mod` | `Package_DFN_QFN.pretty/Texas_RPU0010A_VQFN-HR-10_2x2mm_P0.5mm.kicad_mod` | REJECTED for TPS259474LRPWR; exact package is RPW0010A | PWR-02 eFuse |
| `TI_RGT0016A_VQFN-16_3x3mm_EP1.75x1.75_TPS62130A.kicad_mod` | `Package_DFN_QFN.pretty/QFN-16-1EP_3x3mm_P0.5mm_EP1.75x1.75mm.kicad_mod` | VQFN-16 3x3 EP1.75 (RGT0016A) — TPS62130ARGTR | PWR-04 main buck |

**Validation performed:** all 17 project footprints (these 8 plus the 9 existing manufacturer-derived candidates) parse and export in KiCad 10.0.6 (`kicad-cli fp export svg` against a `.pretty` library directory; 17/17 exported successfully). This is the automated geometry-check row of the DIG-04 acceptance; the **independent second pass against exact-MPN drawings for these 8 remains open** and is deliberately not claimed.

**Deliberately deferred (no fabricated geometry):** GCT USB4105 USB-C receptacle (custom connector; requires drawing-rev B4 comparison, footprint deferred to the EXT-01-class controlled-drawing work), JST BM12B-GHS-TBT expansion header (custom connector; JST drawing comparison required), Alps SKSCLCE010 button (SKSC drawing + enclosure plunger comparison required), ST1633I touch connector (O01-gated), and the T5838 microphone acoustic land (custom 1:1 land + port rules from AUD-01; requires the DS Figure 32/33 CAD comparison). These five remain footprint-open items with their controlling documents already recorded in the subsystem docs.

## 2026-09-23 drawing correction

The [correction record](FOOTPRINT_CORRECTIONS_2026_09_23.md) adds the exact DCU candidate (3.1 mm land-row center spacing), rejects incorrect unpublished DCU/RPW/TCA drafts, and confirms that the original TCA9535 4.4 x 7.8 mm body graphic is correct. The TCA generic land choice and the exact RPW polygon/stencil remain review gates. No generic-package parse result closes these gates.
