pantojinho/StratosCore/references/REUSE_REGISTER.md

# Reference and reuse register

Updated 2026-09-23. The register distinguishes research, original manufacturer-dimension transcriptions, reused KiCad library assets and the separate Claude candidate tooling. See per-source scope below; public access is not permission to relicense. The former generic KiCad W25Q footprint was replaced on 2026-09-17 by an original transcription of Winbond's published land/stencil dimensions. Official license texts are intentionally included under their publication terms.

| Source / exact revision | License evidence | Is reuse permitted? | Use here / modifications |
| --- | --- | --- | --- |
| HAT, ede42aea0a62b0821dacf69886a06be7529f59e8 | Root/tree/API license unestablished; [notes](LEGACY_PROJECTS.md) | Not established for copying; obtain permission | Architecture/pin comparison only; none |
| StratosBrain, 943de16ff35f0b5c77d04f515245bce8342be79b | [MIT](https://github.com/pantojinho/StratosBrain_S3/blob/943de16ff35f0b5c77d04f515245bce8342be79b/LICENSE), copyright CIANDRINI 2026 | MIT-covered code with notices; dependencies/assets separately | Lessons and comparison only; none |
| avBadge, d03f2a3bee7544e03df314edd8eafa24e040701b | Hardware scope unestablished; mixed software subtrees | No copying approved; file-level audit needed | [Architecture study](AVBADGE_NOTES.md); none |
| ADSBee, 2942116b726f3b014605fc78af5373c6452c721d | [GPL v3](https://github.com/PantsForBirds/adsbee/blob/2942116b726f3b014605fc78af5373c6452c721d/LICENSE) and project declaration | Conditional on GPL compliance; not MIT relicensing | [Architecture/PIO study](ADSBEE_NOTES.md); none |
| MeshCore, 0679dbeffc504d562d2f09eb072fdc223f8ffc2a | [Root MIT license](https://github.com/meshcore-dev/MeshCore/blob/0679dbeffc504d562d2f09eb072fdc223f8ffc2a/LICENSE) | Root-covered work with notices; transitive libraries separately | Compatibility objective only; no port/import |
| Junzi Sun, *The 1090 Megahertz Riddle*, online edition | [Published example](https://mode-s.org/1090mhz/content/ads-b/3-airborne-position.html) | Factual captured frame used as a test fixture; no implementation copied | One 14-byte DF17 message retained in independently written host validation; CRC verified locally |
| Manufacturer documentation linked in [source index](../hardware/datasheets/README.md) | Individual vendor copyright/terms | Electrical use and redistribution terms vary; check exact asset | Links, original analysis and dimension transcriptions; 2026-09-23 MMC/BMP/DCU corrections are recorded in docs/FOOTPRINT_CORRECTIONS_2026_09_23.md. No manufacturer PDF or CAD asset redistributed |
| hermes-kicad-pcb, c87e8d450b36224a419c8059fe337d2bf8834551 (2026-09-23) | [MIT](https://github.com/pantojinho/hermes-kicad-pcb/blob/c87e8d450b36224a419c8059fe337d2bf8834551/LICENSE), copyright Gabriel Pantojinho 2026 | Yes, with notice | `candidates/claude-oneshot-revA/tools/schgen.py` independently rewritten from the `sch_gen.py` approach (coordinate transform, `extends` flattening, stub/label drawing); `build_pcb.py` follows its documented netlist-to-board pitfalls. Attribution in the candidate README. Candidate only; baseline untouched |
| KiCad 10.0.6 official symbol/footprint/3D libraries | [CC-BY-SA 4.0 with KiCad library exception](https://www.kicad.org/libraries/license/) | Yes for designs using the libraries | Library symbols/footprints/3D models referenced in the Claude candidate; baseline DIG-04 support footprints also derive from the standard KiCad library, with per-file source provenance in docs/FOOTPRINT_REVIEWS_DIGITAL.md |
| Freerouting 2.4.1 jar (2026) | [GPL-3.0](https://github.com/freerouting/freerouting/blob/master/LICENSE) | Used as an external tool only; not bundled or linked | Autorouting of the one-shot candidate board; routed copper is design output, no Freerouting code in the repository |
| CERN-OHL-P-2.0 / MIT official text | [Provenance and scope](../LICENSES/README.md) | Official published license text used as supplied | License text only; MIT holder/year substituted |

Before importing any asset add: exact URL and commit/revision; file/circuit and destination; copyright holder; SPDX identifier or exact terms; permission evidence; obligations and compatibility decision; modifications; reviewer and date. Include modifications even if the answer is "none." Do not interpret a public repository, a vendor CAD download, or a GPL component running on another MCU as blanket permission.
