pantojinho/StratosCore/docs/DIGITAL_SUPPORT_REVIEW.md

# Digital support parts review

Status: exact engineering candidates reviewed through 2026-09-17. These selections reduce the pre-KiCad queue but remain subject to the recorded footprint/process gates, factory availability and board-level bring-up.

**2026-09-22 (DIG-01): the RP2040 power/reset/BOOTSEL/SWD/oscillator circuit is now specified pin-complete below.** "Pin-complete" means every RP2040 supply, control and support pin has a defined net and value; the schematic capture itself remains Astra work (this document is not a schematic). Sources retrieved and re-extracted 2026-09-22: [RP2040 datasheet](https://datasheets.raspberrypi.com/rp2040/rp2040-datasheet.pdf) (section 1.4 pinout reference, section 2.9 power) and the [hardware design with RP2040](https://datasheets.raspberrypi.com/rp2040/hardware-design-with-rp2040.pdf) (sections 2.1-2.2, 2.4.1, 3.3.2).

## RP2040 power, reset, BOOTSEL, SWD and clock circuit specification (DIG-01)

### Power (pin-complete, values from the Raspberry Pi reference)

| Pin / net group | Count | Net | Decoupling (reference value) |
| --- | --- | --- | --- |
| IOVDD | all IOVDD pins of the QFN-56 | `3V3_MAIN` | 100 nF per power pin, one shared pair allowed on the crowded side exactly as the reference deviates (its C9) — final placement decides |
| USB_VDD | 1 | `3V3_MAIN` (RP2040 USB PHY is on-chip; Rev A routes no RP2040 USB connector — USB service is via ESP32 native USB) | 100 nF |
| ADC_AVDD | 1 | `3V3_MAIN` (Rev A uses no RP2040 ADC function; if a future use appears it must be re-reviewed against ADS-B quiet-rail noise) | 100 nF + 1 nF reference-class filter (reference arrangement) |
| DVDD | all DVDD pins | direct to VREG_VOUT | per reference |
| VREG_VIN | 1 | `3V3_MAIN` | 1 uF ceramic (0402 class) close to the pin |
| VREG_VOUT | 1 | DVDD only | 1 uF ceramic (0402 class) close to the pin; ESR satisfied by small ceramics per reference |

- **Rationale (reference, HWDG sections 2.1.2-2.1.3):** 100 nF per power pin with the two documented deviations; 1 uF at both regulator pins; internal LDO produces the 1.1 V core, so no external 1.1 V rail. RP2040 core/IOVDD current is a PWR-04 inventory input (datasheet section 2.9 figures to be transcribed there — not silently assumed zero).
- **Load-switch interaction (TBD retained):** whether the RP2040 domain switches with the ADS-B digital domain (TPS22918 class) or stays always-on is a SYS-02/off-state-review decision; this specification is rail-source-agnostic, but if switched, the flash-write quiesce ordering recorded above becomes binding.

### Reset and BOOTSEL

- **RUN (active-low global reset): 10 kOhm pull-up to `3V3_MAIN` + 100 nF to GND + wired to a SWD-adjacent test point and to the TCA9535 expander for host-controlled reset.** Datasheet: reset when low, run when high, may be tied to IOVDD if unused — the RC and host control are deliberate Rev A provisions for watchdog-less recovery and DFT access (O28). The expander path is non-safety (GPIO map rule: no safety function on the expander).
- **BOOTSEL recovery (reference arrangement, HWDG section 2.2): QSPI_SS carries the boot strap; 1 kOhm (reference R1) from QSPI_SS to a `USB_BOOT` test point; grounding `USB_BOOT` while toggling RUN enters USB mass-storage boot.** R1 must be populated so the RP2040 can over-drive the applied pull-down when booting normally; the 10 kOhm QSPI_SS pull-up (reference R2) stays DNF per the reference finding with this flash family. `USB_BOOT` and RUN test points are the documented recovery contract for the O28 DFT matrix.
- **No RP2040-side USB connector:** the RP2040 boots as a USB device for programming, but Rev A does not wire a second USB receptacle. Firmware update path: program over SWD from the ESP32 side or a tag-connect-class SWD cable at the test points; the physical access definition belongs to O28/DFT-01. This is an interface disposition, not a new product decision — the GPIO map already reserves no RP2040 USB pins.

### SWD (reference section 3.3.2 + datasheet debug recommendation)

- **SWCLK and SWDIO routed to a 2 x 1 test-point pair (or a 5-pin 1.27 mm Tag-Connect footprint: SWCLK, SWDIO, GND, `3V3_MAIN` sense, RUN) at the board edge.** Datasheet recommends a maximum 24 MHz SWD clock; the pad family and fixture pitch constraints are O28 inputs. No pull resistors required on SWD per the reference minimal design.

### Oscillator (crystal circuit unchanged from the 2026-09-15 review)

- ABM8-272-T3 12 MHz with two 15 pF load capacitors and 1 kOhm series damping at XOUT, per the Raspberry Pi recommendation already recorded; XIN/XOUT short and symmetric; requalification rule on any IOVDD change stands.

### Corner test plan (DIG-01 closure evidence)

Bring-up level (post-PCBA, declared as such): (1) cold boot at 3.3 V +/-5% across the accepted temperature corners; (2) repeated RUN reset with flash-write quiesce verified (reset-reason register readback); (3) full-image programming over SWD and checksum verify; (4) BOOTSEL entry via the `USB_BOOT` point from a powered-off and a running state; (5) oscillator startup time and timebase comparison against GNSS PPS. Pre-Astra deliverable remains the testable specification above; measurements are board-stage evidence per the workboard boundary.

## RP2040 boot flash

`W25Q128JVSIQ` is the preferred RP2040 boot-flash candidate. Raspberry Pi's current *Hardware design with RP2040* uses the Winbond `W25Q128JVS` family in its minimal design, and RP2040 supports up to 16 MB of external QSPI flash. The exact `W25Q128JVSIQ` provides 128 Mbit/16 MB, 2.7-3.6 V operation, industrial -40 to 85 °C rating and an 8-SOIC package. The larger package is deliberate for Rev A inspectability and rework; a smaller suffix would require a separate footprint and availability review.

The project footprint now transcribes Winbond Rev-M package/pin data and `AN0000009` Rev 2.1 copper/stencil geometry. Its corrected 1.90 x 0.80 mm copper and distinct 1.80 x 0.70 mm paste apertures passed an independent dimensional second pass and KiCad 10 export on 2026-09-17. Assembler mask/courtyard approval and boot/reset/program/temperature bring-up remain.

Route the six QSPI signals directly between RP2040 and flash, keep them short, follow the Raspberry Pi reference pullup/decoupling arrangement and expose the documented BOOTSEL recovery path. The previously open items are now closed from the primary sources (reviewed 2026-09-17):

- **Ordering code:** Winbond W25Q128JV Rev M ordering table confirms `W25Q128JVSIQ` = 128 Mbit, SOIC-8 208-mil, industrial-plus-style `IQ` speed/temperature grade with 133 MHz fast-read support (VCC 3.0-3.6 V; 2.7-3.6 V operation limits fast read to 104 MHz).
- **Quad mode:** the QE bit is non-volatile in Status Register-2; QE=1 makes /WP→IO2 and /HOLD→IO3 (Rev M section 7.1.4). RP2040 quad-XIP boot requires QE set; the Raspberry Pi reference found the external QSPI_SS pull-up unnecessary with this device (R2 = 10 kΩ DNF in the reference design).
- **BOOTSEL strap:** QSPI_SS doubles as the boot strap; the reference uses R1 = 1 kΩ from QSPI_SS to a `USB_BOOT` header, and BOOTSEL is entered by grounding it while toggling RUN (active-low reset, pulled high on-board). R1 must be present so RP2040 can safely over-drive the applied pull-down when booting.
- **Maximum XIP clock:** bootrom ENTER_XIP uses a conservative 03h serial read; the SSI SCKDV divider scales the QSPI clock from the system clock, so 3.3 V operation allows up to 133 MHz flash commands with margin — final XIP speed is a firmware/bring-up setting, not a hardwire.
- **Power-cut write integrity:** W25Q128JV Rev M §8.2.19 warns that data in the page/sector/block under an erase or program operation — including a *suspended* one — may become corrupted on accidental power interruption, and the Reset-command section requires checking BUSY/SUS before any device reset. RP2040 §2.12 provides POR, brown-out detection, supply monitor, external reset and a Source-of-Last-Reset register. Consequence for the off-state review (O05/O06/gate 9): a switched RP2040 domain must guarantee firmware quiesces flash writes (BUSY/SUS clear) before the TPS22918 rail falls — QOD discharge ordering and the host-visible reset reason are the review items, not a resistor value.

Bring-up must prove cold boot, repeated reset, full-image programming, checksum and operation across the accepted temperature and voltage range.

## RP2040 reference clock

`ABM8-272-T3` is the preferred 12 MHz crystal. Raspberry Pi explicitly recommends this exact Abracon part at 3.3 V and documents 30 ppm tolerance/stability, 50 ohm maximum ESR and 10 pF load capacitance. Its reference circuit uses two 15 pF load capacitors and a 1 kohm series damping resistor. Preserve that starting circuit and keep XIN/XOUT traces short and symmetric; any part/value or IOVDD change requires oscillator startup and drive-level requalification.

The project footprint now uses the exact Abracon 1.30 x 0.70 mm lands at X = +/-1.15 mm and Y = +/-0.875 mm; the earlier generic 1.4 x 1.2 mm land was rejected. The 1:1 mask/paste remains an assembler-approved process starting point. This clock is required for deterministic ADS-B capture timing and reliable USB/debug behavior. Test startup at voltage and temperature corners and compare the RP2040 timebase against GNSS PPS before accepting timing performance.

## microSD socket

`DM3AT-SF-PEJM5` is the preferred socket candidate. Hirose's May 2026 DM3 catalog identifies the exact part as an eight-contact, top-board, right-angle SMT, push-push microSD socket with a card-detection switch. The official product page gives a 13.85 x 15.95 mm body, 1.68 mm height, 0.5 A rating, gold-plated contacts and 10,000 mating cycles; official 2D/3D files are available.

Use the already budgeted shared SPI interface for Rev A. Route card detect to a slow I2C-expander input; no safety function depends on it. Add separately selected ESD protection, required SD pullups and a reviewed load switch if power cycling is retained. The exact drawing `0000947170 / EDC-325165-00-00` Rev 4 was compared on 2026-09-15. Electrical contacts, card detect and shell-land placement match. The drawing's C0.15 +/-0.05 terminal feature lies inside the correct rectangular PCB land. The footprint now marks the 11.0 mm operational card envelope, 0.8 mm inward overstroke edge at Y = 8.925, locked edge at Y = 9.725 and ejected edge at Y = 13.725 on `Cmts.User`. The socket must sit at the enclosure edge; assembler paste approval and final enclosure access/clearance remain before KiCad release.

### microSD circuit specification (DIG-02, 2026-09-22)

Worker-level circuit closure feeding DIG-04's remaining-footprint pass and the O28/DFT-01 access list. Sources: Raspberry Pi hardware design guide section 3.3 (SD interface; retrieved 2026-09-22), the DM3 exact drawing/catalog already cited above, and the shared-SPI contract in [the GPIO map](INTERFACE_GPIO_MAP.md).

**Power:**

- **VDD:** switched `3V3_SD` domain behind the P11 `SD_SW_EN_N` enable (DIG-03 corrected polarity: OFF at power-up and expander fault; firmware raises the enable). Rationale: write-integrity power-fail ordering with the W25Q flash-write quiesce rule (flash section above) and runtime power profiles; SD is not needed in every profile.
- **Bulk/output capacitance:** 10 uF + 100 nF on `3V3_SD` at the socket (reference-class value for SD card insertion surge; final value re-checked in PWR-04 against the TPS22918 current limit and insertion inrush).
- **Power-fail behavior (design rule, board-stage proof retained):** TPS22918-class QOD discharge dumps `3V3_SD` when the enable drops or the rail upstream fails; ESP32 firmware must treat an SD absent-ACK after re-enable as a fresh card init, never a resumed session. The flash-write quiesce ordering (RP2040) is unaffected: RP2040 flash is not on `3V3_SD`.
- **Card current inventory input:** insertion/operation peak is a PWR-04 row (datasheet-class 100-200 mA write allowance already flagged in the matrix's 3V3_MAIN subtotal as 200 mA planning) — not re-invented here.

**Signals (all `3V3_SD` domain; the card is the only load):**

- CLK, CMD, DAT0-3: shared-SPI mapping per the GPIO map contract. **SPI-mode pin mapping:** ESP32 CLK -> card CLK, MOSI -> CMD, MISO -> DAT0, and `SD_CS` (GPIO14, dedicated) -> **DAT3, which is the SPI-mode chip select**; DAT2 is unused by the card in SPI mode (card-internal pull only).
- **Push-pull vs open-drain:** ESP32-S3 SPI controller drives push-pull; no open-drain bus emulation is used, so the SD-specification 10-90 kohm card-internal pull-ups on CMD/DAT are relied on for card-side lines, and **no host-side pull-ups are fitted on CLK** (reference: pull-ups on CLK are discouraged — they can clock the card while the host is powered down or the rail is off).
- **Host-side 10 kohm pull-ups:** CMD and DAT0 only, **pulled to `3V3_SD`, not `3V3_MAIN`** — pulling to the always-on rail would feed the unpowered card/socket through the card's internal diodes when the domain is off (back-power path). DAT3/CS carries a 10 kohm pull-up to `3V3_SD` as well (keeps the card deselected while the host boots or the rail rises); DAT1-2 keep only the card-internal pulls since they are inactive in SPI mode.
- **Card detect:** DM3 switch to GND, 100 kohm on-board pull-up on the expander input side per the DIG-03 map (P00, `3V3_MAIN` domain — the switch contacts are rated for it and the pin is read-only).
- **ESD:** the socket is user-accessible (enclosure edge), so the card signal lines get protection at the socket — one 4-channel `TPD4E05U06DQARG4`-family array (0.5 pF class, USON-10) covering CLK/CMD/DAT0/DAT3, and CD covered by its 100 kohm pull with an optional 100 ohm series resistor (slow, read-only line); placement at the connector with short strike paths (DIG-04 footprint and the system-level-ESD-only caveat from PWR-02 apply verbatim: no system-level kV rating is claimed).

**Enclosure access (mechanical interface, MECH-02 boundary):** the socket sits at the PCB/enclosure edge with the 11.0 mm operational card envelope and the ejection stroke already marked on `Cmts.User`; the printed dummy must prove card insertion/removal clearance with the enclosure wall and confirm the push-push overstroke does not foul the wall (MECH-03 test, not closable here).

**DFT hooks handed to O28/DFT-01:** `3V3_SD` rail measure point (current, for PWR-04/O13), CD test point, and the shared-SPI lines are covered by the existing bus test provisions.

**Remaining TBD (explicit):** final ESD array MPN confirmation against its current data sheet at purchase; insertion-surge value into PWR-04; assembler paste disposition (SNS-01/EXT-05 class gate).

## Availability snapshots

Checked 2026-09-14 for prototype planning only:

| Part | Snapshot | Consequence |
| --- | --- | --- |
| `W25Q128JVSIQ` | DigiKey displayed 57,555 in stock at USD 4.21 quantity one | Strong prototype availability; recheck reel/PCBA sourcing |
| `ABM8-272-T3` | DigiKey displayed 29,393 in stock at USD 0.71 quantity one | Exact Raspberry Pi recommendation remains practical |
| `DM3AT-SF-PEJM5` | DigiKey regional pages displayed about 29,700 in stock and about USD 5.20 quantity one | Mechanically robust but relatively expensive; do not substitute without controlled-drawing review |

Primary evidence: [Raspberry Pi hardware design guide](https://datasheets.raspberrypi.com/rp2040/hardware-design-with-rp2040.pdf), [Winbond W25Q128JV Rev M](https://www.winbond.com/resource-files/W25Q128JV%20RevM%2012242024%20Plus.pdf), [Winbond AN0000009 Rev 2.1](https://www.winbond.com/resource-files/AN0000009%20SpiFlash%20PCB%20Layout%20Guideline%20v2.1%2006122020.pdf), [Hirose exact product page](https://www.hirose.com/product/p/CL0609-0031-0-00) and [Hirose DM3 May 2026 catalog](https://www.hirose.com/en/product/document?documentid=D49662_en&documenttype=Catalog&lang=en&series=DM3). Distributor snapshots: [DigiKey flash](https://www.digikey.com/en/products/detail/winbond-electronics/W25Q128JVSIQ/5803943), [DigiKey crystal](https://www.digikey.com/en/products/detail/abracon-llc/ABM8-272-T3/22472366) and [DigiKey socket](https://www.digikey.com/en/products/detail/hirose-electric-co-ltd/DM3AT-SF-PEJM5/2533565).

## Related support selections

Preferred candidates for the microphone/translator, USB-C/signal ESD, expansion connector, buttons, slow-control expander and rail regulators are now recorded in [the audio review](AUDIO_ARCHITECTURE.md), [connector review](CONNECTOR_ARCHITECTURE.md), [control-I/O review](CONTROL_IO_REVIEW.md) and [power rail plan](POWER_RAIL_PLAN.md). Their exact footprints, applications and board-level tests remain open. microSD media, USB VBUS protection and several power-safety parts still have no selected MPN.
