pantojinho/StratosCore/candidates/claude-oneshot-revA/docs/review_notes/TPS62130A_RGT_FOOTPRINT.md

# TPS62130A (U7) RGT footprint audit

Review date: 2026-09-23. Scope: the comparison candidate's TPS62130A land (`U7`, PWR-04 main buck) against TI's current package drawing. This note is a candidate review record, not a release approval. No `.kicad_pcb` or `.kicad_sch` file was changed.

## Sources
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
