pantojinho/StratosCore/candidates/claude-oneshot-revA/images/enclosure_front.png

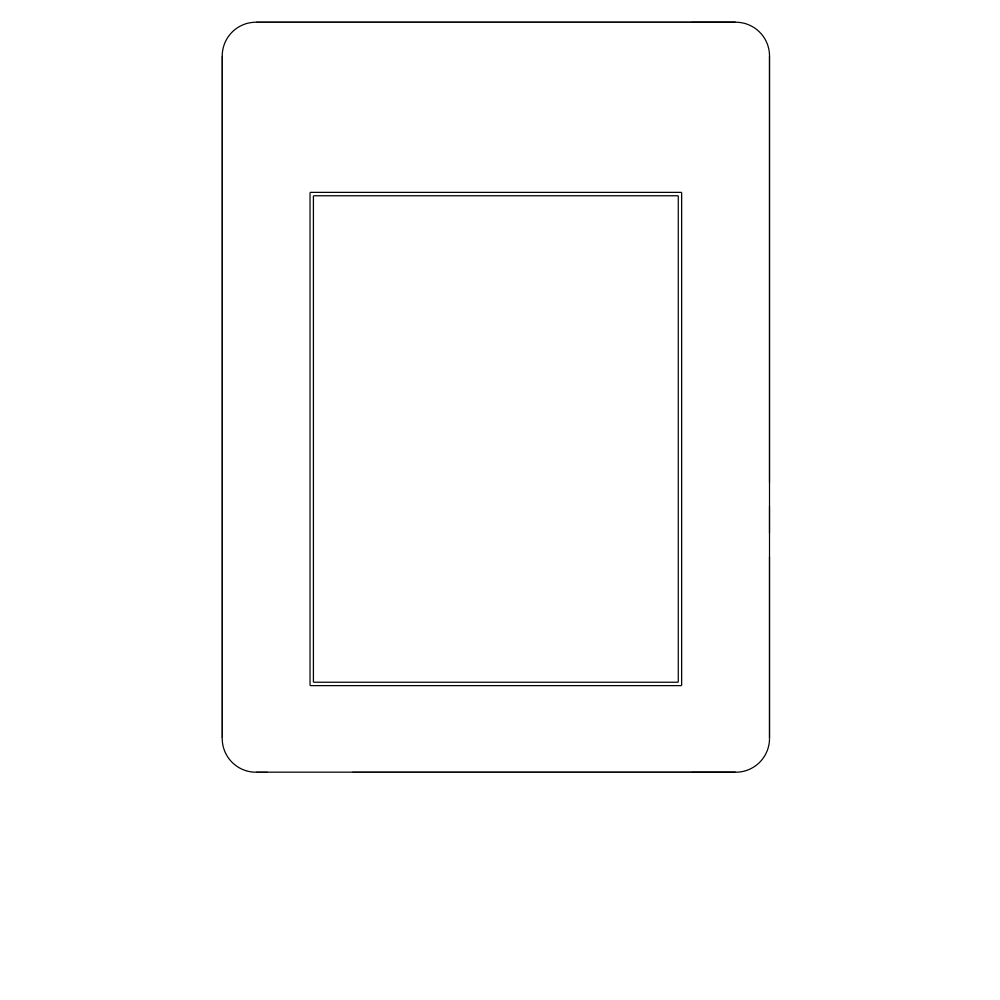
candidates/claude-oneshot-revA/images/enclosure_front.png
