pantojinho/StratosCore/candidates/claude-oneshot-revA/images/enclosure_side.png

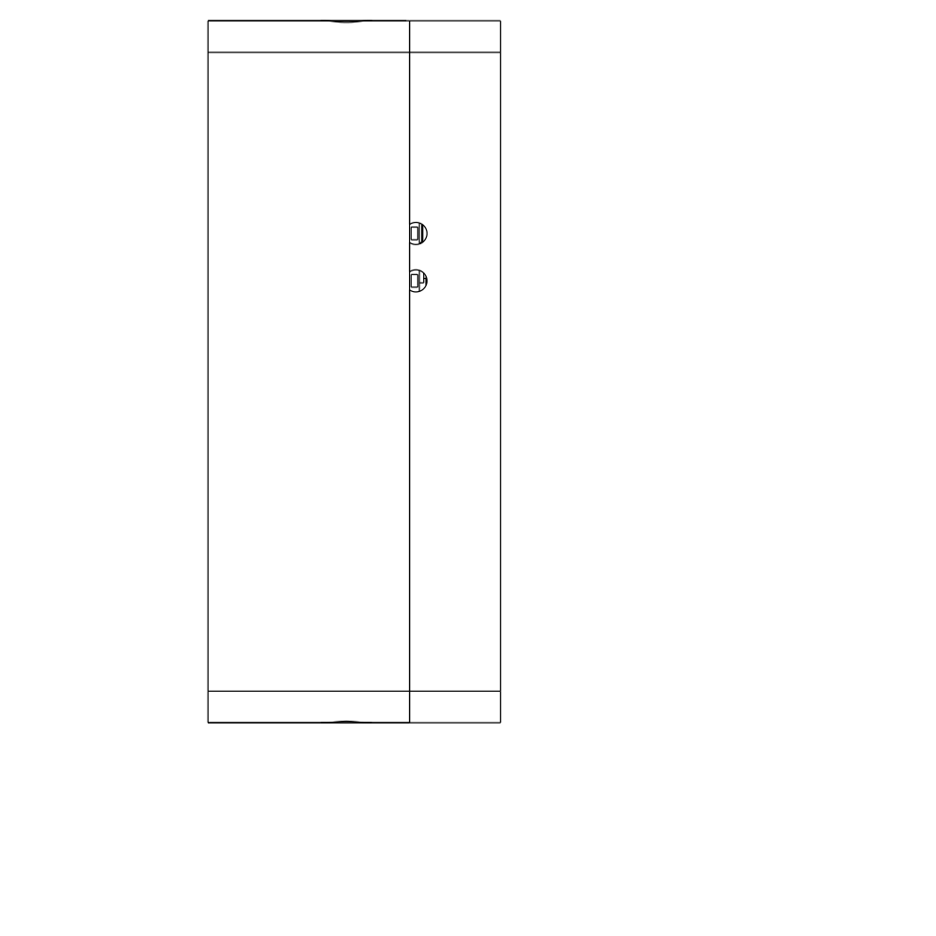
candidates/claude-oneshot-revA/images/enclosure_side.png
