pantojinho/StratosCore/candidates/claude-oneshot-revA/outputs/render_bottom.png

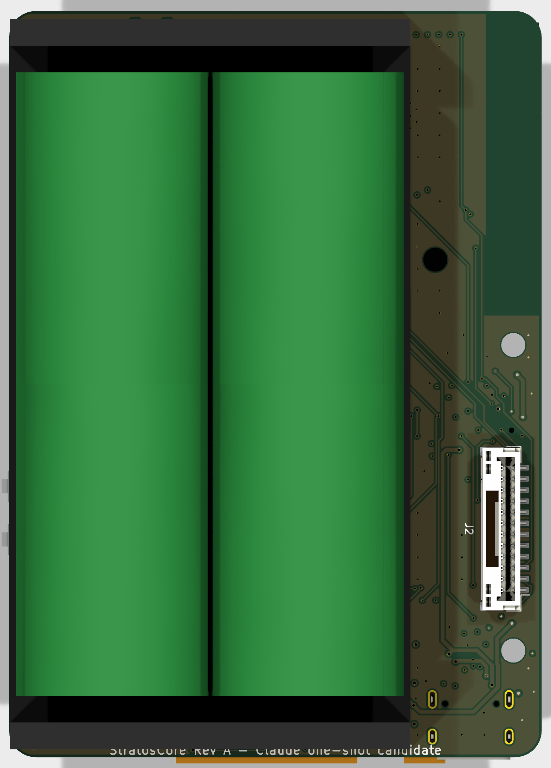
candidates/claude-oneshot-revA/outputs/render_bottom.png
