pantojinho/StratosCore/candidates/claude-oneshot-revA/outputs/render_top.png

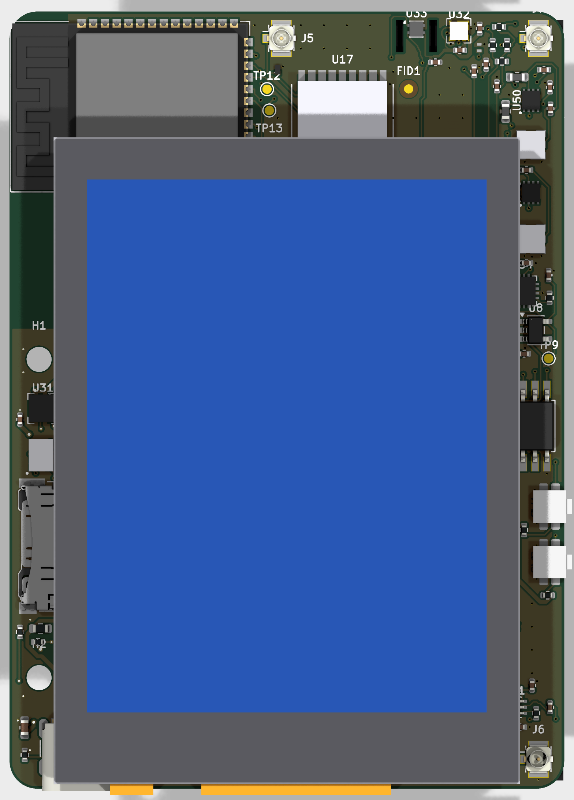
candidates/claude-oneshot-revA/outputs/render_top.png
