pantojinho/StratosCore/candidates/claude-oneshot-revA/outputs/bom_candidate.csv

Refs | Value | Footprint | MPN | Status | Source | Qty | DNP
BT1 | 2S 21700 holder (MPN TBD) | SC:BatteryHolder_2S_21700_TBD | TBD | OWNER DIRECTION - MPN/REVIEW TBD |  | 1
C1,C2 | 1uF 25V X7R | Capacitor_SMD:C_0603_1608Metric |  |  |  | 2
C3,C30,C35-C37,C42,C43,C51-C54,C57,C61-C63,C72,C97,C100-C107,C110-C113,C116,C122,C125,C126 | 100nF | Capacitor_SMD:C_0402_1005Metric |  | ADC_AVDD,USB_VDD |  | 33
C9 | TBD (O06) | Capacitor_SMD:C_0402_1005Metric |  | ITIMER value TBD at O06 |  | 1 | DNP
C10 | 1uF 25V | Capacitor_SMD:C_0603_1608Metric |  |  |  | 1
C11 | 10uF 25V | Capacitor_SMD:C_0805_2012Metric |  |  |  | 1
C12,C95,C96 | 47nF | Capacitor_SMD:C_0402_1005Metric |  |  |  | 3
C13,C55 | 4.7uF 10V | Capacitor_SMD:C_0603_1608Metric |  |  |  | 2
C14,C15 | 22uF 16V | Capacitor_SMD:C_0805_2012Metric |  |  |  | 2
C16 | 10uF 16V | Capacitor_SMD:C_0805_2012Metric |  |  |  | 1
C20 | 10uF 25V X7R | Capacitor_SMD:C_0805_2012Metric |  |  |  | 1
C21 | 100nF 25V | Capacitor_SMD:C_0402_1005Metric |  |  |  | 1
C22,C23 | 22uF 6.3V X7R | Capacitor_SMD:C_0805_2012Metric |  | second output cap; DC-bias review |  | 2
C24,C25 | 3.3nF | Capacitor_SMD:C_0402_1005Metric |  | feed-forward per repo text; review |  | 2
C26-C29,C34,C40,C108,C109,C124 | 1uF | Capacitor_SMD:C_0402_1005Metric |  | VREG_VIN,VREG_VOUT |  | 9
C31 | 2.2uF | Capacitor_SMD:C_0402_1005Metric |  |  |  | 1
C32 | 10nF | Capacitor_SMD:C_0402_1005Metric |  | VDDIO decoupling (DS) |  | 1
C33,C41,C44,C50,C70,C91,C121 | 10uF | Capacitor_SMD:C_0603_1608Metric |  | SET/RESET capacitor per DS |  | 7
C56 | 1uF 50V X7R | Capacitor_SMD:C_0805_2012Metric |  |  |  | 1
C60 | 1uF X7R | Capacitor_SMD:C_0402_1005Metric |  |  |  | 1
C71,C73 | 470nF | Capacitor_SMD:C_0402_1005Metric |  | VREG decoupling; value per E449 BOM TBD |  | 2
C74-C80,C83 | TBD (E449) | Capacitor_SMD:C_0402_1005Metric |  | DC block to PE4259 RF1; value TBD,RX balun series C; value TBD,RX balun shunt; value TBD,TX match shunt; value TBD,VR_PA decoupling; value TBD,antenna DC block; value TBD,pi-filter shunt; value TBD |  | 8
C81,C82 | 1nF | Capacitor_SMD:C_0402_1005Metric |  | AN1200.40 C14,AN1200.40 C15 |  | 2
C88 | 100nF | Capacitor_SMD:C_0402_1005Metric |  |  |  | 1 | DNP
C90,C98,C120,C123,C800,C802,C840,C842 | 100pF | Capacitor_SMD:C_0402_1005Metric |  | BLB01 EVB C1,BLB01 EVB C4 |  | 8
C99 | 1nF | Capacitor_SMD:C_0402_1005Metric |  | basic value 1nF slows pulses; DNP pending bench |  | 1 | DNP
C114,C115 | 15pF C0G | Capacitor_SMD:C_0402_1005Metric |  |  |  | 2
C127 | 100nF X7R | Capacitor_SMD:C_0402_1005Metric |  | DS: 0.1uF at pin 7 |  | 1
C801,C803,C841,C843 | 12pF | Capacitor_SMD:C_0402_1005Metric |  | BLB01 EVB C2 (RF out),BLB01 EVB C3 |  | 4
D1 | 60V Schottky TBD | Diode_SMD:D_SOD-123F |  | exact 60 V-class part TBD (open) |  | 1
D2 | TPD1E0B04DPYR | SC:TI_TPD1E0B04DPYR_X1SON-2_DPY0002A | TPD1E0B04DPYR |  |  | 1
D3 | TPD1E0B04DPYR (option) | SC:TI_TPD1E0B04DPYR_X1SON-2_DPY0002A |  | ESD option at ADS-B input - DNP until RF review |  | 1 | DNP
F1 | TBD (O05) | Fuse:Fuse_1206_3216Metric |  | Rating/type TBD by qualified review (O05) |  | 1
FL1,FL2 | TA2003A 1090MHz SAW | SC:TAI-SAW_TA2003A_SMD-6_3.0x3.0mm | TA2003A |  |  | 2
J1 | USB4105-GF-A | Connector_USB:USB_C_Receptacle_GCT_USB4105-xx-A_16P_TopMnt_Horizontal | USB4105-GF-A | PREFERRED CANDIDATE - drawing B4 second pass open | https://gct.co/files/drawings/usb4105.pdf | 1
J2 | BM12B-GHS-TBT (expansion) | Connector_JST:JST_GH_BM12B-GHS-TBT_1x12-1MP_P1.25mm_Vertical | BM12B-GHS-TBT | pinout = CONNECTOR_ARCHITECTURE.md; ESD/hot-plug TBD |  | 1
J3 | XF3M-4015-1B (TFT 40p FPC) | SC:Omron_XF3M-4015-1B_1x40-1MP_P0.5mm_Horizontal | XF3M-4015-1B | SAMPLE/CONTROLLED-DRAWING HOLD (O01); footprint from Omron G146-E1 lands |  | 1
J4 | XF3M-0615-1B (CTP 6p FPC) | SC:Omron_XF3M-0615-1B_1x06-1MP_P0.5mm_Horizontal | XF3M-0615-1B | SAMPLE HOLD; ST1633I address 0x70 convention open |  | 1
J5 | U.FL-R-SMT-1(60) GNSS | SC:Hirose_U.FL-R-SMT-1_60_Vertical | U.FL-R-SMT-1(60) |  |  | 1
J6 | U.FL-R-SMT-1(60) LoRa | SC:Hirose_U.FL-R-SMT-1_60_Vertical | U.FL-R-SMT-1(60) |  |  | 1
J7 | U.FL-R-SMT-1(60) ADS-B | SC:Hirose_U.FL-R-SMT-1_60_Vertical | U.FL-R-SMT-1(60) |  |  | 1
J8 | DM3AT-SF-PEJM5 | SC:Hirose_DM3AT-SF-PEJM5_microSD_HC | DM3AT-SF-PEJM5 |  | Hirose drawing 0000947170 Rev 4 | 1
L1 | 1uH (DFE252012F-1R0 class) | Inductor_SMD:L_1008_2520Metric |  | TI Fig.69 value; saturation/DCR review |  | 1
L2 | 2.2uH XFL4020-222MEB | SC:L_Coilcraft_XxL4020 | XFL4020-222MEB |  |  | 1
L3 | 10uH LPS4018-103MRC | SC:L_Coilcraft_LPS4018 | LPS4018-103MRC |  |  | 1
L70 | 15uH (DC-DC) | Inductor_SMD:L_0805_2012Metric |  | AN1200.40 L7 15uH; exact part/ISAT TBD |  | 1
L71-L74 | TBD (E449) | Inductor_SMD:L_0402_1005Metric |  | PA supply choke VR_PA->RFO; value TBD,RX balun series L; value TBD,TX match/notch series; value TBD,pi-filter series; value TBD |  | 4
L800,L840 | 27nH | Inductor_SMD:L_0603_1608Metric |  | BLB01 EVB L1 |  | 2
L801,L841 | 82nH | Inductor_SMD:L_0603_1608Metric |  | BLB01 EVB L2 |  | 2
MK1 | MMICT5838-00-012 | SC:TDK_T5838_LGA-7_3.5x2.65mm_BottomPort | MMICT5838-00-012 | PREFERRED CANDIDATE - acoustic/footprint review |  | 1
Q1 | Dual N-MOSFET TBD (O05) | Package_TO_SOT_SMD:SOT-23-6 |  | PLACEHOLDER - FET selection/SOA/package TBD (O05) |  | 1
Q2 | 2N7002 | Package_TO_SOT_SMD:SOT-23 |  |  |  | 1
R1,R53-R55,R96,R801,R841 | 0R | Resistor_SMD:R_0402_1005Metric |  | BLB01 EVB R2,GPIO8 host control of translator OE (optional),Shield/chassis treatment TBD,unused RD tie TBD,unused WR(D/CX) tie TBD |  | 7
R2,R8 | 232k 1% | Resistor_SMD:R_0402_1005Metric |  | one-shot candidate |  | 2
R3,R5,R9,R29 | 100k 1% | Resistor_SMD:R_0402_1005Metric |  | one-shot candidate |  | 4
R4 | 442k 1% | Resistor_SMD:R_0402_1005Metric |  |  |  | 1
R6 | 1.69k 1% | Resistor_SMD:R_0402_1005Metric |  |  |  | 1
R7,R11-R13,R20,R21,R27,R30,R46-R48,R51,R57,R70,R90,R100,R104-R106 | 100k | Resistor_SMD:R_0402_1005Metric |  | P10 default released,default OFF,default OFF (DIG-03),fail-safe: charge disabled |  | 19
R10 | 900k 1% | Resistor_SMD:R_0402_1005Metric |  | data-sheet 900k |  | 1
R14 | 300R | Resistor_SMD:R_0603_1608Metric |  | TI reverse-bottom-cell limiter |  | 1
R15 | TBD (RCBSET) | Resistor_SMD:R_2512_6332Metric |  | balance current TBD; 40.8R/0.41W at 100 mA planning point |  | 1
R16 | 5.23k 1% | Resistor_SMD:R_0402_1005Metric |  |  |  | 1
R17 | 30.1k 1% | Resistor_SMD:R_0402_1005Metric |  |  |  | 1
R18 | 2.21k 1% | Resistor_SMD:R_0402_1005Metric |  | IINMAX = 1110/2210 = 502 mA (default-current floor) |  | 1
R19,R22-R24,R40-R42,R45,R50,R52,R58,R91,R101-R103 | 10k | Resistor_SMD:R_0402_1005Metric |  | PSEL high = low input-current class |  | 15
R26 | 0R | Resistor_SMD:R_0402_1005Metric |  | SERVICE OVERRIDE ONLY - DNP |  | 1 | DNP
R28 | 312k 1% | Resistor_SMD:R_0402_1005Metric |  |  |  | 1
R31,R32,R49 | 0R | Resistor_SMD:R_0603_1608Metric |  | GNSS branch; bead DCR<=0.15R fallback (GNSS-01),TFT VCC link (O01 power clarification),expansion current limit TBD |  | 3
R43,R44,R98 | 2.2k 1% | Resistor_SMD:R_0402_1005Metric |  | ADSB-01 |  | 3
R56 | 2.21R 1% 0.1W | Resistor_SMD:R_0603_1608Metric |  |  |  | 1
R60,R61 | 470R | Resistor_SMD:R_0402_1005Metric |  | ABLIC Table 11 typ,ABLIC Table 11 typ; R1*C1 = R2*C2 |  | 2
R62 | 2k | Resistor_SMD:R_0402_1005Metric |  | ABLIC Table 11 typ |  | 1
R71,R72 | 100R | Resistor_SMD:R_0402_1005Metric |  | AN1200.40 R3,AN1200.40 R4 |  | 2
R86,R87 | TBD (OWN-09) | Resistor_SMD:R_0402_1005Metric |  | threshold divider BLOCKED by OWN-09 |  | 2
R88 | 10k | Resistor_SMD:R_0402_1005Metric |  | optional RP2040 PWM threshold |  | 1 | DNP
R92,R93 | 1k | Resistor_SMD:R_0402_1005Metric |  | BOOTSEL strap (DIG-01) |  | 2
R95 | 52.3R 1% | Resistor_SMD:R_0402_1005Metric |  | ADI basic connections R1 |  | 1
R97 | TBD (TADJ @1090 MHz) | Resistor_SMD:R_0402_1005Metric |  | value from ADI TADJ table TBD |  | 1
R800,R840 | 6.8k | Resistor_SMD:R_0402_1005Metric |  | BLB01 EVB R1 |  | 2
SW1 | SKSCLCE010 (BUTTON_1 / BOOT) | SC:SW_Alps_SKSCLCE010_SidePush | SKSCLCE010 | footprint from SKSC drawing - review |  | 1
SW2 | SKSCLCE010 (BUTTON_2) | SC:SW_Alps_SKSCLCE010_SidePush | SKSCLCE010 | footprint from SKSC drawing - review |  | 1
TH1 | 10k NTC (103AT class, TBD) | Resistor_SMD:R_0603_1608Metric |  | thermal coupling to cells TBD |  | 1
U1 | ESP32-S3-WROOM-1-N16R8 | RF_Module:ESP32-S3-WROOM-1 | ESP32-S3-WROOM-1-N16R8 | LOCKED | Espressif ESP32-S3-WROOM-1 datasheet | 1
U2,U23 | TPD4E05U06DQAR | Package_SON:USON-10_2.5x1.0mm_P0.5mm | TPD4E05U06DQARG4 |  | TI SLVSBO7O | 2
U3 | TPS259474LRPWR | SC:TI_RPW0010A_VQFN-HR-10_2x2mm_P0.45mm | TPS259474LRPWR | CANDIDATE - O05/O06 review | TI SLVSFC9C | 1
U4 | TUSB320LAIRWBR | SC:TI_RWB0012B_X2QFN-12_1.6x1.6mm_TUSB320LAI | TUSB320LAIRWBR |  | TI SLLSEQ8D (pin map identical to KiCad TUSB320 symbol) | 1
U5 | S-8252 (product code TBD, O05) | Package_TO_SOT_SMD:SOT-23-6 |  | CANDIDATE FAMILY - TOPOLOGY CONFLICT - QUALIFIED REVIEW (O05) | ABLIC S-8252 Rev 4.0 Fig.14/Table 11 | 1
U6 | BQ25887RGER | Package_DFN_QFN:Texas_RGE0024H_VQFN-24-1EP_4x4mm_P0.5mm_EP2.7x2.7mm | BQ25887RGER | PREFERRED CANDIDATE - SAFETY REVIEW (O05) | TI SLUSD89B | 1
U7 | TPS62130ARGTR | SC:TI_RGT0016C_VQFN-16_3x3mm_EP1.68x1.68_TPS62130A | TPS62130ARGTR |  | TI SLVSAG7F | 1
U8 | TPS7A2030PDBVR | SC:TI_DBV0005A_SOT-23-5_TPS7A20 | TPS7A2030PDBVR |  | TI SBVS338H | 1
U9 | TPS7A2018PDBVR | SC:TI_DBV0005A_SOT-23-5_TPS7A20 | TPS7A2018PDBVR |  | TI SBVS338H | 1
U10-U12 | TPS22918DBVR | SC:TI_DBV0006A_SOT-23-6_TPS22918 | TPS22918DBVR | AUD-02 proposed branch; CT/QOD/ramp review open | TI SLVSD76C | 3
U13 | TCA9535PWR | SC:TI_PW0024A_TSSOP-24_4.4x7.8mm_TCA9535 | TCA9535PWR |  | TI SCPS201F; port map DIG-03 + one-shot spares | 1
U14 | SN74AXC4T245PWR | Package_SO:TSSOP-16_4.4x5mm_P0.65mm | SN74AXC4T245PWR |  | TI SCES877B; DSP-02 | 1
U15 | SN74LVC1G07DBVR | Package_TO_SOT_SMD:SOT-23-5 | SN74LVC1G07DBVR |  | TI SCES296AG 7.4 | 1
U16 | TPS61169DCKR | SC:TI_DCK0005A_SC-70-5_TPS61169 | TPS61169DCKR |  | TI SNVSA40B | 1
U17 | MAX-M10S-00B | SC:u-blox_MAX-M10S-00B_LCC-18_10.1x9.7mm | MAX-M10S-00B | LOCKED | u-blox UBX-22035176 R08 | 1
U20 | RP2040 | Package_DFN_QFN:QFN-56-1EP_7x7mm_P0.4mm_EP3.2x3.2mm | RP2040 | LOCKED | RP2040 datasheet + Hardware design with RP2040 | 1
U21 | W25Q128JVSIQ | SC:Winbond_W25Q128JVSIQ_SOIC-8_5.3x5.3mm_P1.27mm | W25Q128JVSIQ |  | Winbond Rev M | 1
U24 | TXU0202DCUR | SC:TI_DCU0008A_VSSOP-8_2.3x2mm_P0.5mm_TXU0202 | TXU0202DCUR |  | TI SCES942A (DCU = VSSOP-8 2.3x2.0 mm) | 1
U30 | ICM-42688-P | SC:TDK_ICM-42688-P_LGA-14_3x2.5mm_P0.5mm | ICM-42688-P | LOCKED - assembler mask/paste gate | TDK DS-000347 v1.9 | 1
U31 | MMC5983MA | SC:MEMSIC_MMC5983MA_LGA-16_3x3mm_P0.5mm_CORRECTED | MMC5983MA | LOCKED - magnetic placement review | MEMSIC MMC5983MA Rev A | 1
U32 | BMP581 | SC:Bosch_BMP581_LGA-10_2x2mm_CORRECTED | BMP581 | LOCKED (D29 indicative backup) | Bosch BST-BMP581-DS004-13 | 1
U33 | SHT40-AD1B-R2 | SC:Sensirion_DFN-4_1.5x1.5mm_P0.8mm_SHT4x_NoCentralPad | SHT40-AD1B-R2 | LOCKED | Sensirion SHT4x v7.3 | 1
U40 | SX1262IMLTRT | Package_DFN_QFN:QFN-24-1EP_4x4mm_P0.5mm_EP2.6x2.6mm | SX1262IMLTRT | LOCKED | Semtech SX1261/2 DS Rev 1.2; EP numbered 25 in KiCad (pin 0 in DS) | 1
U41 | PE4259 | Package_TO_SOT_SMD:SOT-363_SC-70-6 | PE4259 | PROPOSED (AN1200.40 reference switch); RF1/RF2 vs CTRL polarity to confirm in firmware | pSemi DOC-03694 | 1
U50,U52 | BLB01 | SC:BeRex_BLB01_DFN-8-1EP_2x2mm_P0.5mm | BLB01 | PROPOSED - prototype required | BeRex BLB01 rev 6.6 | 2
U54 | ADL5513ACPZ-R7 | Package_CSP:LFCSP-16-1EP_3x3mm_P0.5mm_EP1.7x1.7mm | ADL5513ACPZ-R7 | PROPOSED - EP land TBD (CP-16-22) | ADI ADL5513 Rev B | 1
U55 | MCP6566T-E/OT | Package_TO_SOT_SMD:SOT-23-5 | MCP6566T-E/OT |  | Microchip DS20002143G base map | 1
Y1 | 12MHz ABM8-272-T3 | SC:Abracon_ABM8-272-T3_Crystal_SMD_3225-4Pin_3.2x2.5mm | ABM8-272-T3 |  |  | 1
Y2 | 32 MHz (CL 10pF) MPN TBD | Crystal:Crystal_SMD_2016-4Pin_2.0x1.6mm |  | MPN TBD |  | 1
