pantojinho/StratosCore/hardware/kicad/01_compute.kicad_sch

## KiCad design hardware/kicad/01_compute.kicad_sch (2026-09-11)

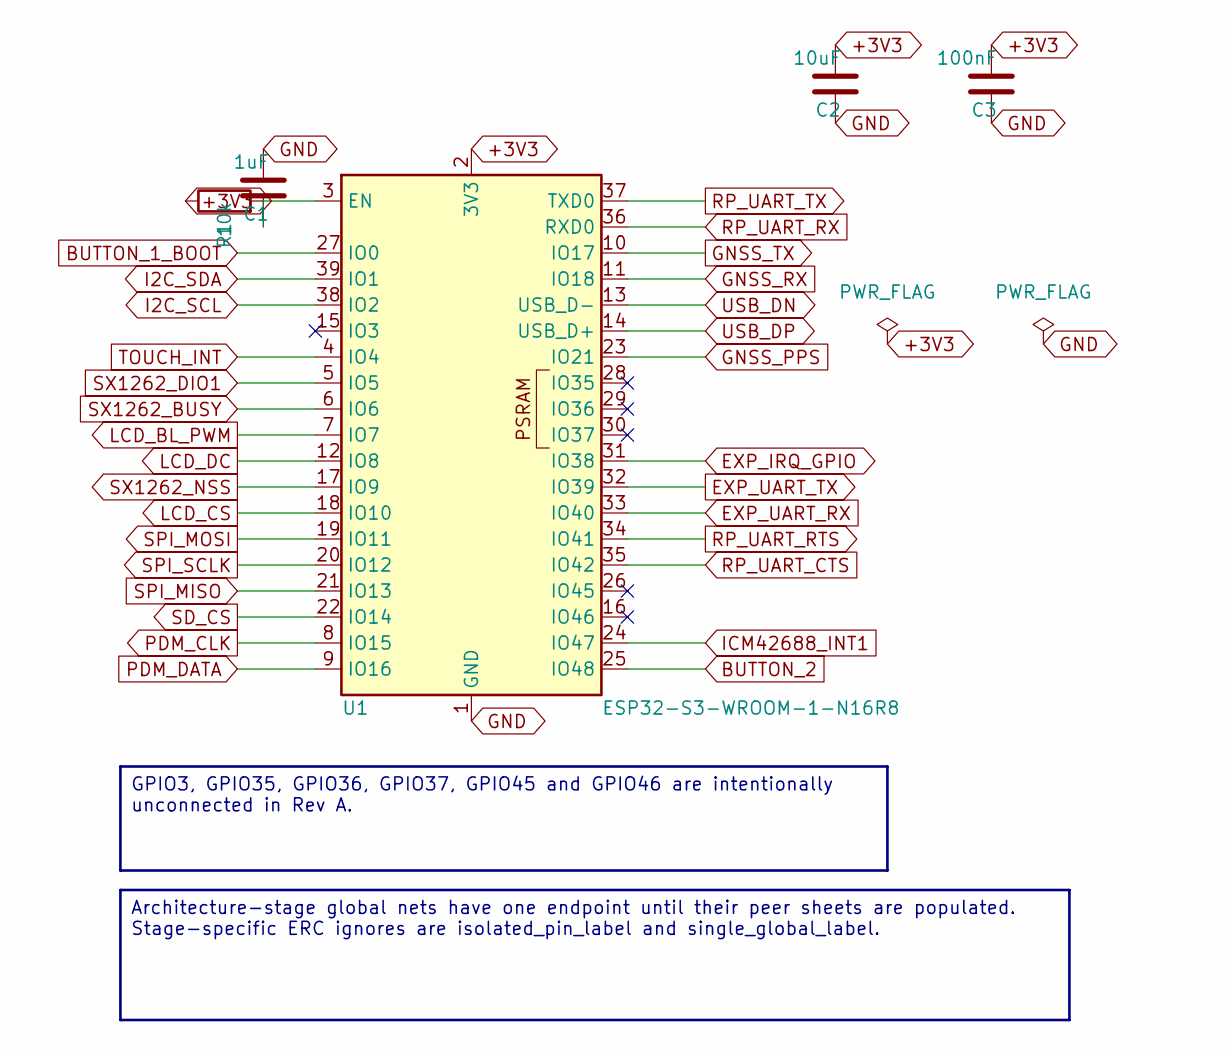
[picture p57: schematic 01_compute.kicad_sch]

Parts:
C1: 1uF; C_0603_1608Metric
C2: 10uF; C_0603_1608Metric
C3: 100nF; C_0603_1608Metric
R1: 10k; R_0603_1608Metric
U1: ESP32-S3-WROOM-1-N16R8; ESP32-S3-WROOM-1

Connections:
+3V3: C2.2, C3.2, R1.1, U1.2 (3V3)
BUTTON_1_BOOT: U1.27 (IO0)
BUTTON_2: U1.25 (IO48)
EXP_IRQ_GPIO: U1.31 (IO38)
EXP_UART_RX: U1.33 (IO40)
EXP_UART_TX: U1.32 (IO39)
GND: C1.2, C2.1, C3.1, U1.1 (GND), U1.40 (GND), U1.41 (GND)
GNSS_PPS: U1.23 (IO21)
GNSS_RX: U1.11 (IO18)
GNSS_TX: U1.10 (IO17)
I2C_SCL: U1.38 (IO2)
I2C_SDA: U1.39 (IO1)
ICM42688_INT1: U1.24 (IO47)
LCD_BL_PWM: U1.7 (IO7)
LCD_CS: U1.18 (IO10)
LCD_DC: U1.12 (IO8)
unnamed: C1.1, R1.2, U1.3 (EN)
PDM_CLK: U1.8 (IO15)
PDM_DATA: U1.9 (IO16)
RP_UART_CTS: U1.35 (IO42)
RP_UART_RTS: U1.34 (IO41)
RP_UART_RX: U1.36 (RXD0)
RP_UART_TX: U1.37 (TXD0)
SD_CS: U1.22 (IO14)
SPI_MISO: U1.21 (IO13)
SPI_MOSI: U1.19 (IO11)
SPI_SCLK: U1.20 (IO12)
SX1262_BUSY: U1.6 (IO6)
SX1262_DIO1: U1.5 (IO5)
SX1262_NSS: U1.17 (IO9)
TOUCH_INT: U1.4 (IO4)
USB_DN: U1.13 (USB_D-)
USB_DP: U1.14 (USB_D+)

Notes on the sheet:
GPIO3, GPIO35, GPIO36, GPIO37, GPIO45 and GPIO46 are intentionally unconnected in Rev A.
Architecture-stage global nets have one endpoint until their peer sheets are populated. Stage-specific ERC ignores are isolated_pin_label and single_global_label.
