pantojinho/StratosCore/hardware/kicad/04_sensors.kicad_sch

## KiCad design hardware/kicad/04_sensors.kicad_sch (2026-09-16)

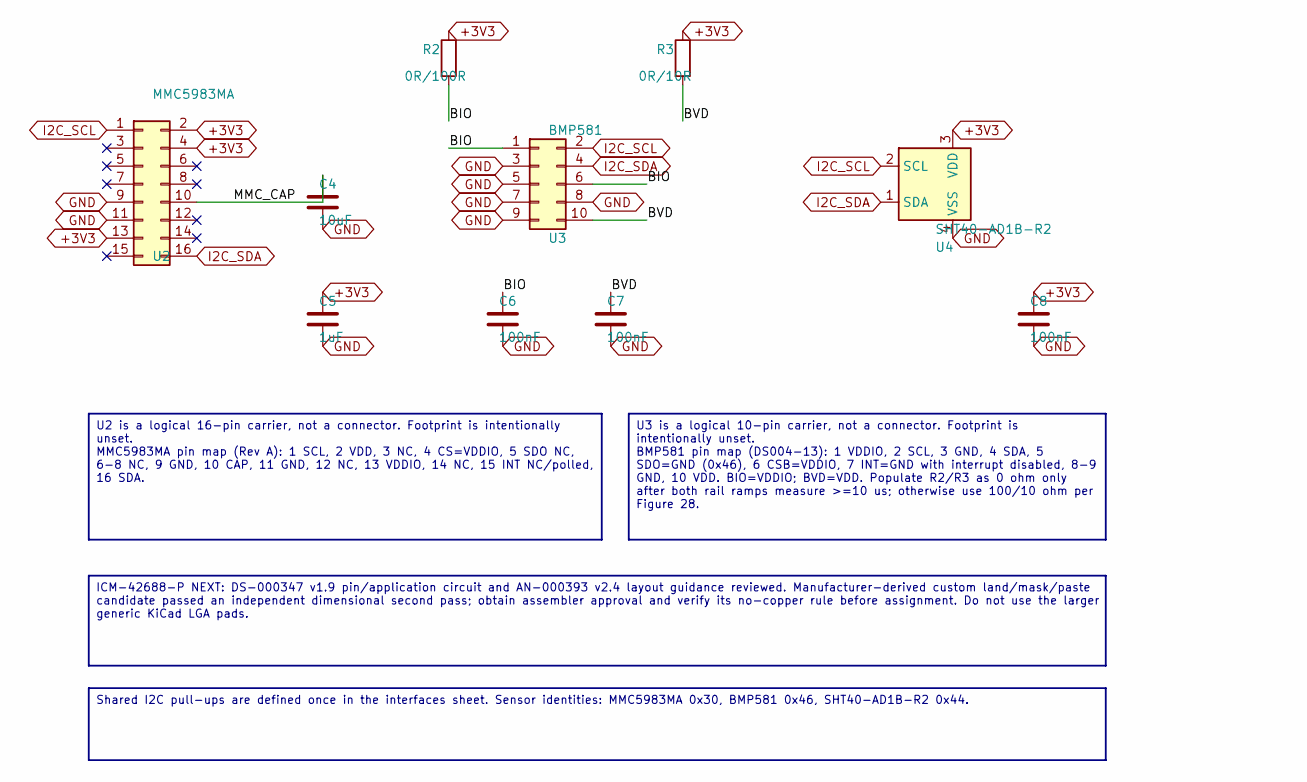
[picture p58: schematic 04_sensors.kicad_sch]

Parts:
C4: 10uF; C_0805_2012Metric
C5: 1uF; C_0603_1608Metric
C6, C7, C8: 100nF; C_0603_1608Metric
R2: 0R/100R; R_0603_1608Metric
R3: 0R/10R; R_0603_1608Metric
U2: MMC5983MA
U3: BMP581
U4: SHT40-AD1B-R2; Sensirion_DFN-4_1.5x1.5mm_P0.8mm_SHT4x_NoCentralPad

Connections:
+3V3: C5.2, C8.2, R2.1, R3.1, U2.2, U2.4, U2.13, U4.3 (VDD)
BIO: C6.2, R2.2, U3.1, U3.6
BVD: C7.2, R3.2, U3.10
GND: C4.1, C5.1, C6.1, C7.1, C8.1, U2.9, U2.11, U3.3, U3.5, U3.7, U3.8, U3.9, U4.4 (VSS)
I2C_SCL: U2.1, U3.2, U4.2 (SCL)
I2C_SDA: U2.16, U3.4, U4.1 (SDA)
MMC_CAP: C4.2, U2.10

Notes on the sheet:
U2 is a logical 16-pin carrier, not a connector. Footprint is intentionally unset. MMC5983MA pin map (Rev A): 1 SCL, 2 VDD, 3 NC, 4 CS=VDDIO, 5 SDO NC, 6-8 NC, 9 GND, 10 CAP, 11 GND, 12 NC, 13 VDDIO, 14 NC, 15 INT NC/polled, 16 SDA.
U3 is a logical 10-pin carrier, not a connector. Footprint is intentionally unset. BMP581 pin map (DS004-13): 1 VDDIO, 2 SCL, 3 GND, 4 SDA, 5 SDO=GND (0x46), 6 CSB=VDDIO, 7 INT=GND with interrupt disabled, 8-9 GND, 10 VDD. BIO=VDDIO; BVD=VDD. Populate R2/R3 as 0 ohm only after both rail ramps measu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
ICM-42688-P NEXT: DS-000347 v1.9 pin/application circuit and AN-000393 v2.4 layout guidance reviewed. Manufacturer-derived custom land/mask/paste candidate passed an independent dimensional second pass; obtain assembler approval and verify its no-copper rule before assignment. Do not use the larger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
Shared I2C pull-ups are defined once in the interfaces sheet. Sensor identities: MMC5983MA 0x30, BMP581 0x46, SHT40-AD1B-R2 0x44.
